pennyarcade/minidragon/schematics/Layout/A Register.kicad_sch

## KiCad design schematics/Layout/A Register.kicad_sch (2026-05-20)

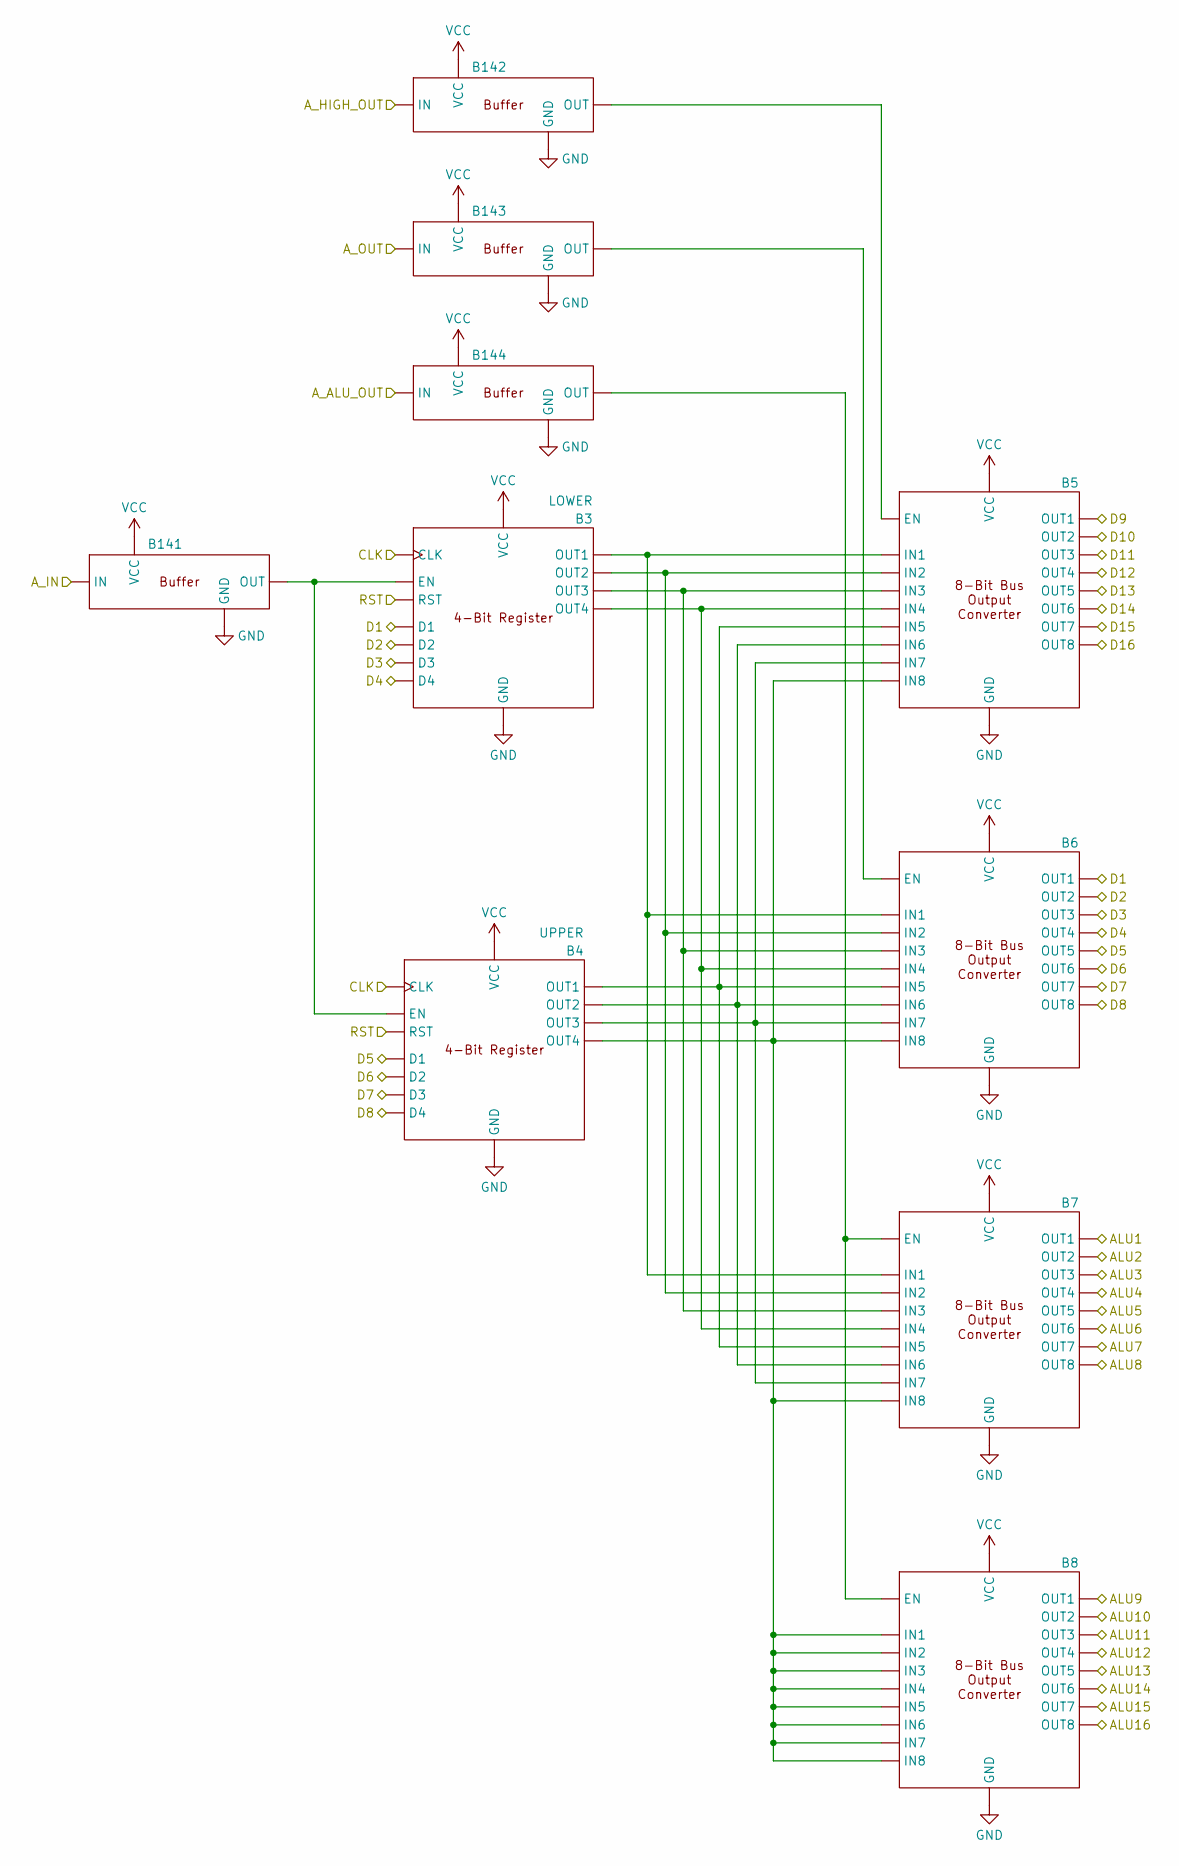
[picture p16: schematic A Register.kicad_sch]

Parts:
B3: LOWER
B4: UPPER
B5, B6, B7, B8, B141, B142, B143, B144: (no value)

Connections:
ALU1: B7.
ALU2: B7.
ALU3: B7.
ALU4: B7.
ALU5: B7.
ALU6: B7.
ALU7: B7.
ALU8: B7.
ALU9: B8.
ALU10: B8.
ALU11: B8.
ALU12: B8.
ALU13: B8.
ALU14: B8.
ALU15: B8.
ALU16: B8.
A_ALU_OUT: B144.
A_HIGH_OUT: B142.
A_IN: B141.
A_OUT: B143.
CLK: B3., B4.
D1: B3., B6.
D2: B3., B6.
D3: B3., B6.
D4: B3., B6.
D5: B4., B6.
D6: B4., B6.
D7: B4., B6.
D8: B4., B6.
D9: B5.
D10: B5.
D11: B5.
D12: B5.
D13: B5.
D14: B5.
D15: B5.
D16: B5.
GND: B3., B4., B5., B6., B7., B8., B141., B142., B143., B144.
unnamed: B3., B5., B6., B7.
unnamed: B4., B5., B6., B7., B8.
unnamed: B3., B4., B141.
unnamed: B5., B142.
unnamed: B6., B143.
unnamed: B7., B8., B144.
RST: B3., B4.
VCC: B3., B4., B5., B6., B7., B8., B141., B142., B143., B144.
