pennyarcade/minidragon/schematics/Layout/ALU Add Circuit.kicad_sch

## KiCad design schematics/Layout/ALU Add Circuit.kicad_sch (2026-05-20)

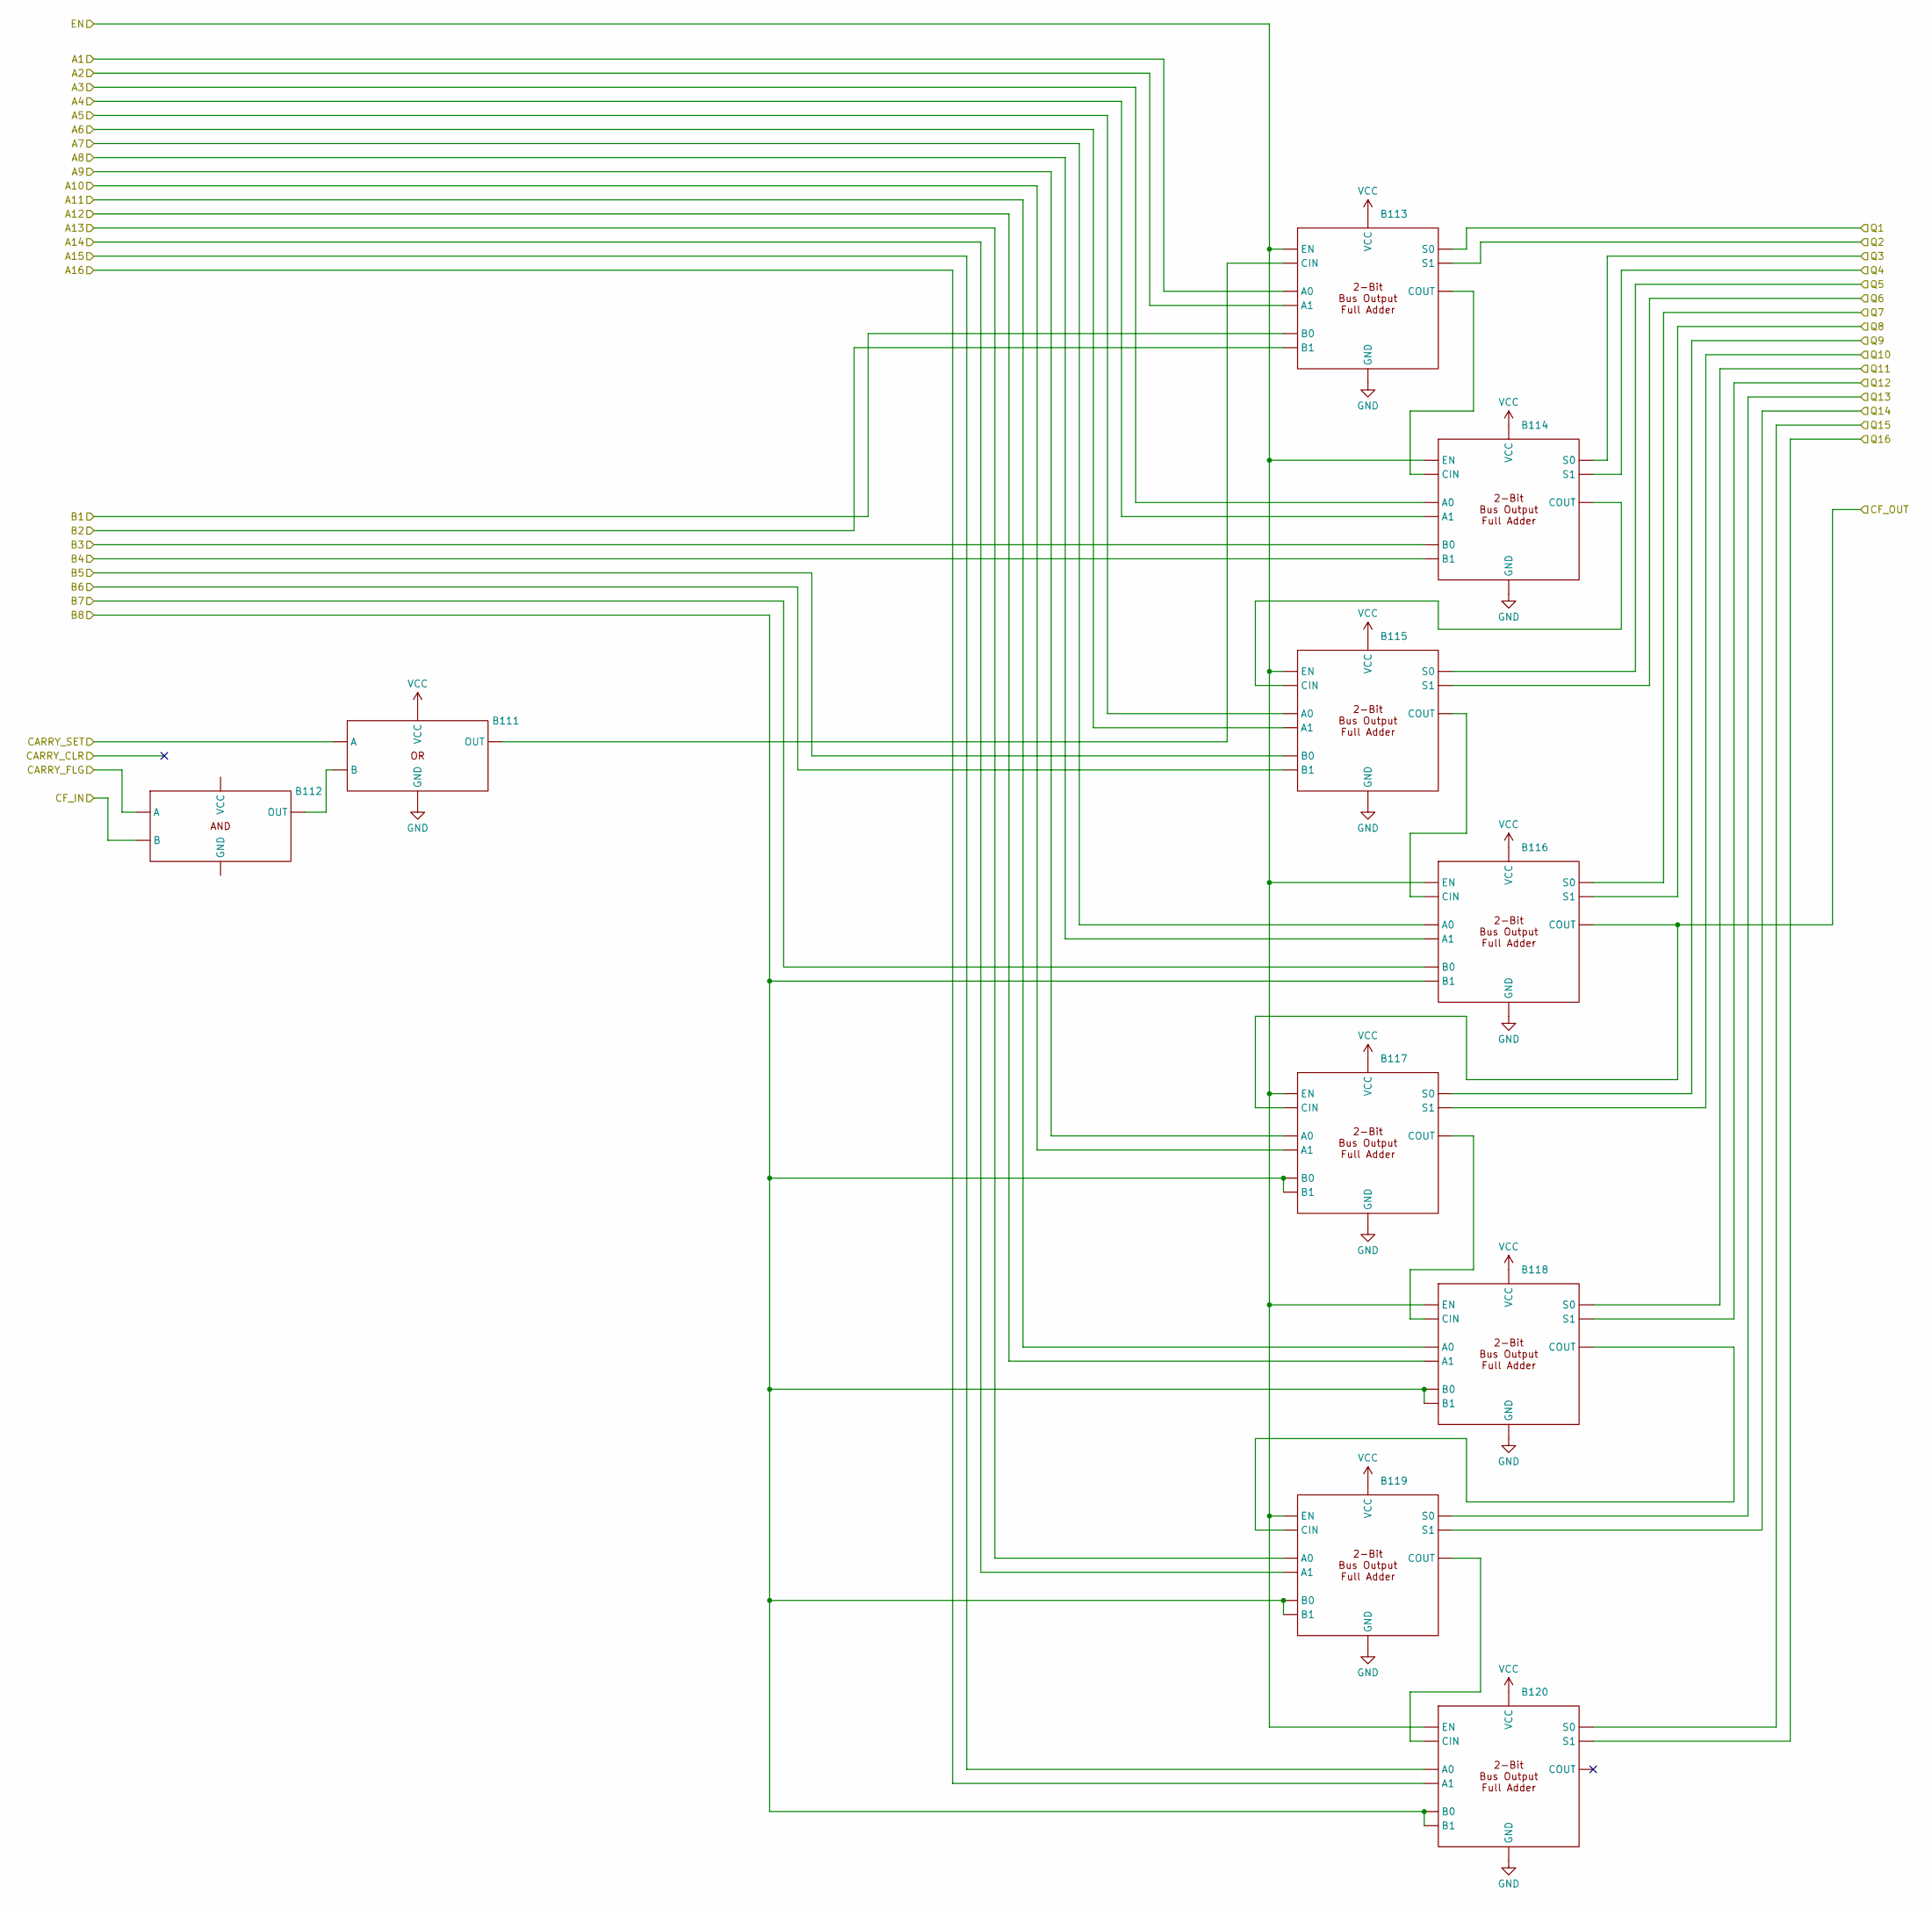
[picture p18: schematic ALU Add Circuit.kicad_sch]

Parts:
B111, B112, B113, B114, B115, B116, B117, B118, B119, B120: (no value)

Connections:
A1: B113.
A2: B113.
A3: B114.
A4: B114.
A5: B115.
A6: B115.
A7: B116.
A8: B116.
A9: B117.
A10: B117.
A11: B118.
A12: B118.
A13: B119.
A14: B119.
A15: B120.
A16: B120.
B1: B113.
B2: B113.
B3: B114.
B4: B114.
B5: B115.
B6: B115.
B7: B116.
B8: B116., B117., B118., B119., B120.
CARRY_FLG: B112.
CARRY_SET: B111.
CF_IN: B112.
CF_OUT: B116., B117.
EN: B113., B114., B115., B116., B117., B118., B119., B120.
GND: B111., B113., B114., B115., B116., B117., B118., B119., B120.
unnamed: B111., B112., B113.
unnamed: B113., B114.
unnamed: B114., B115.
unnamed: B115., B116.
unnamed: B117., B118.
unnamed: B118., B119.
unnamed: B119., B120.
Q1: B113.
Q2: B113.
Q3: B114.
Q4: B114.
Q5: B115.
Q6: B115.
Q7: B116.
Q8: B116.
Q9: B117.
Q10: B117.
Q11: B118.
Q12: B118.
Q13: B119.
Q14: B119.
Q15: B120.
Q16: B120.
VCC: B111., B113., B114., B115., B116., B117., B118., B119., B120.
