pennyarcade/minidragon/schematics/Layout/ALU Boolean Circuit.kicad_sch

## KiCad design schematics/Layout/ALU Boolean Circuit.kicad_sch (2026-05-20)

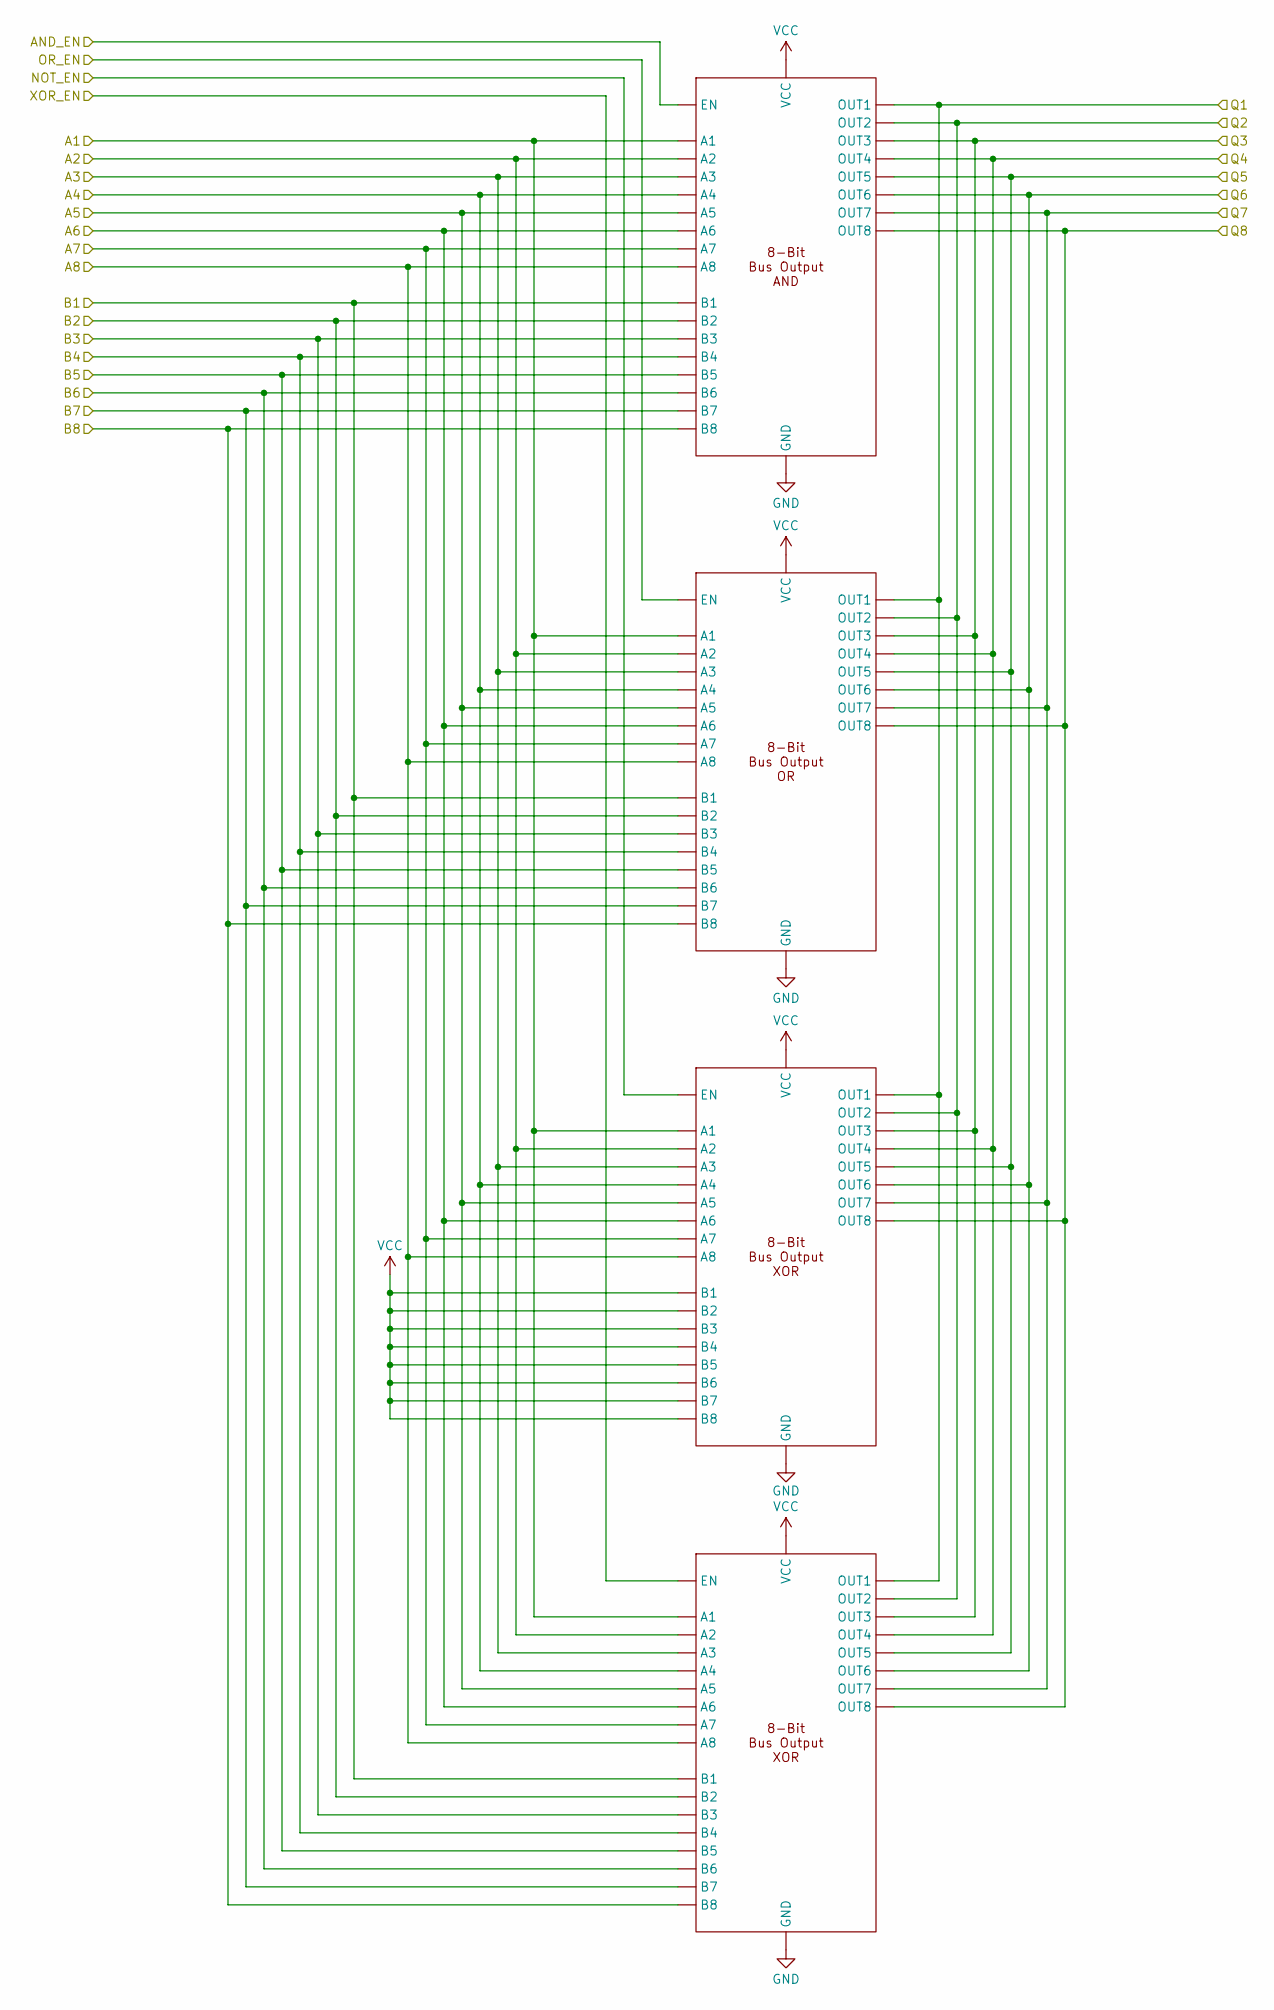
[picture p19: schematic ALU Boolean Circuit.kicad_sch]

Parts:
B158, B159, B160, B161: (no value)

Connections:
A1: B158., B159., B160., B161.
A2: B158., B159., B160., B161.
A3: B158., B159., B160., B161.
A4: B158., B159., B160., B161.
A5: B158., B159., B160., B161.
A6: B158., B159., B160., B161.
A7: B158., B159., B160., B161.
A8: B158., B159., B160., B161.
AND_EN: B158.
B1: B158., B159., B161.
B2: B158., B159., B161.
B3: B158., B159., B161.
B4: B158., B159., B161.
B5: B158., B159., B161.
B6: B158., B159., B161.
B7: B158., B159., B161.
B8: B158., B159., B161.
GND: B158., B159., B160., B161.
NOT_EN: B160.
OR_EN: B159.
Q1: B158., B159., B160., B161.
Q2: B158., B159., B160., B161.
Q3: B158., B159., B160., B161.
Q4: B158., B159., B160., B161.
Q5: B158., B159., B160., B161.
Q6: B158., B159., B160., B161.
Q7: B158., B159., B160., B161.
Q8: B158., B159., B160., B161.
VCC: B158., B159., B160., B161.
XOR_EN: B161.
