pennyarcade/minidragon/schematics/Layout/ALU.kicad_sch

## KiCad design schematics/Layout/ALU.kicad_sch (2026-05-20)

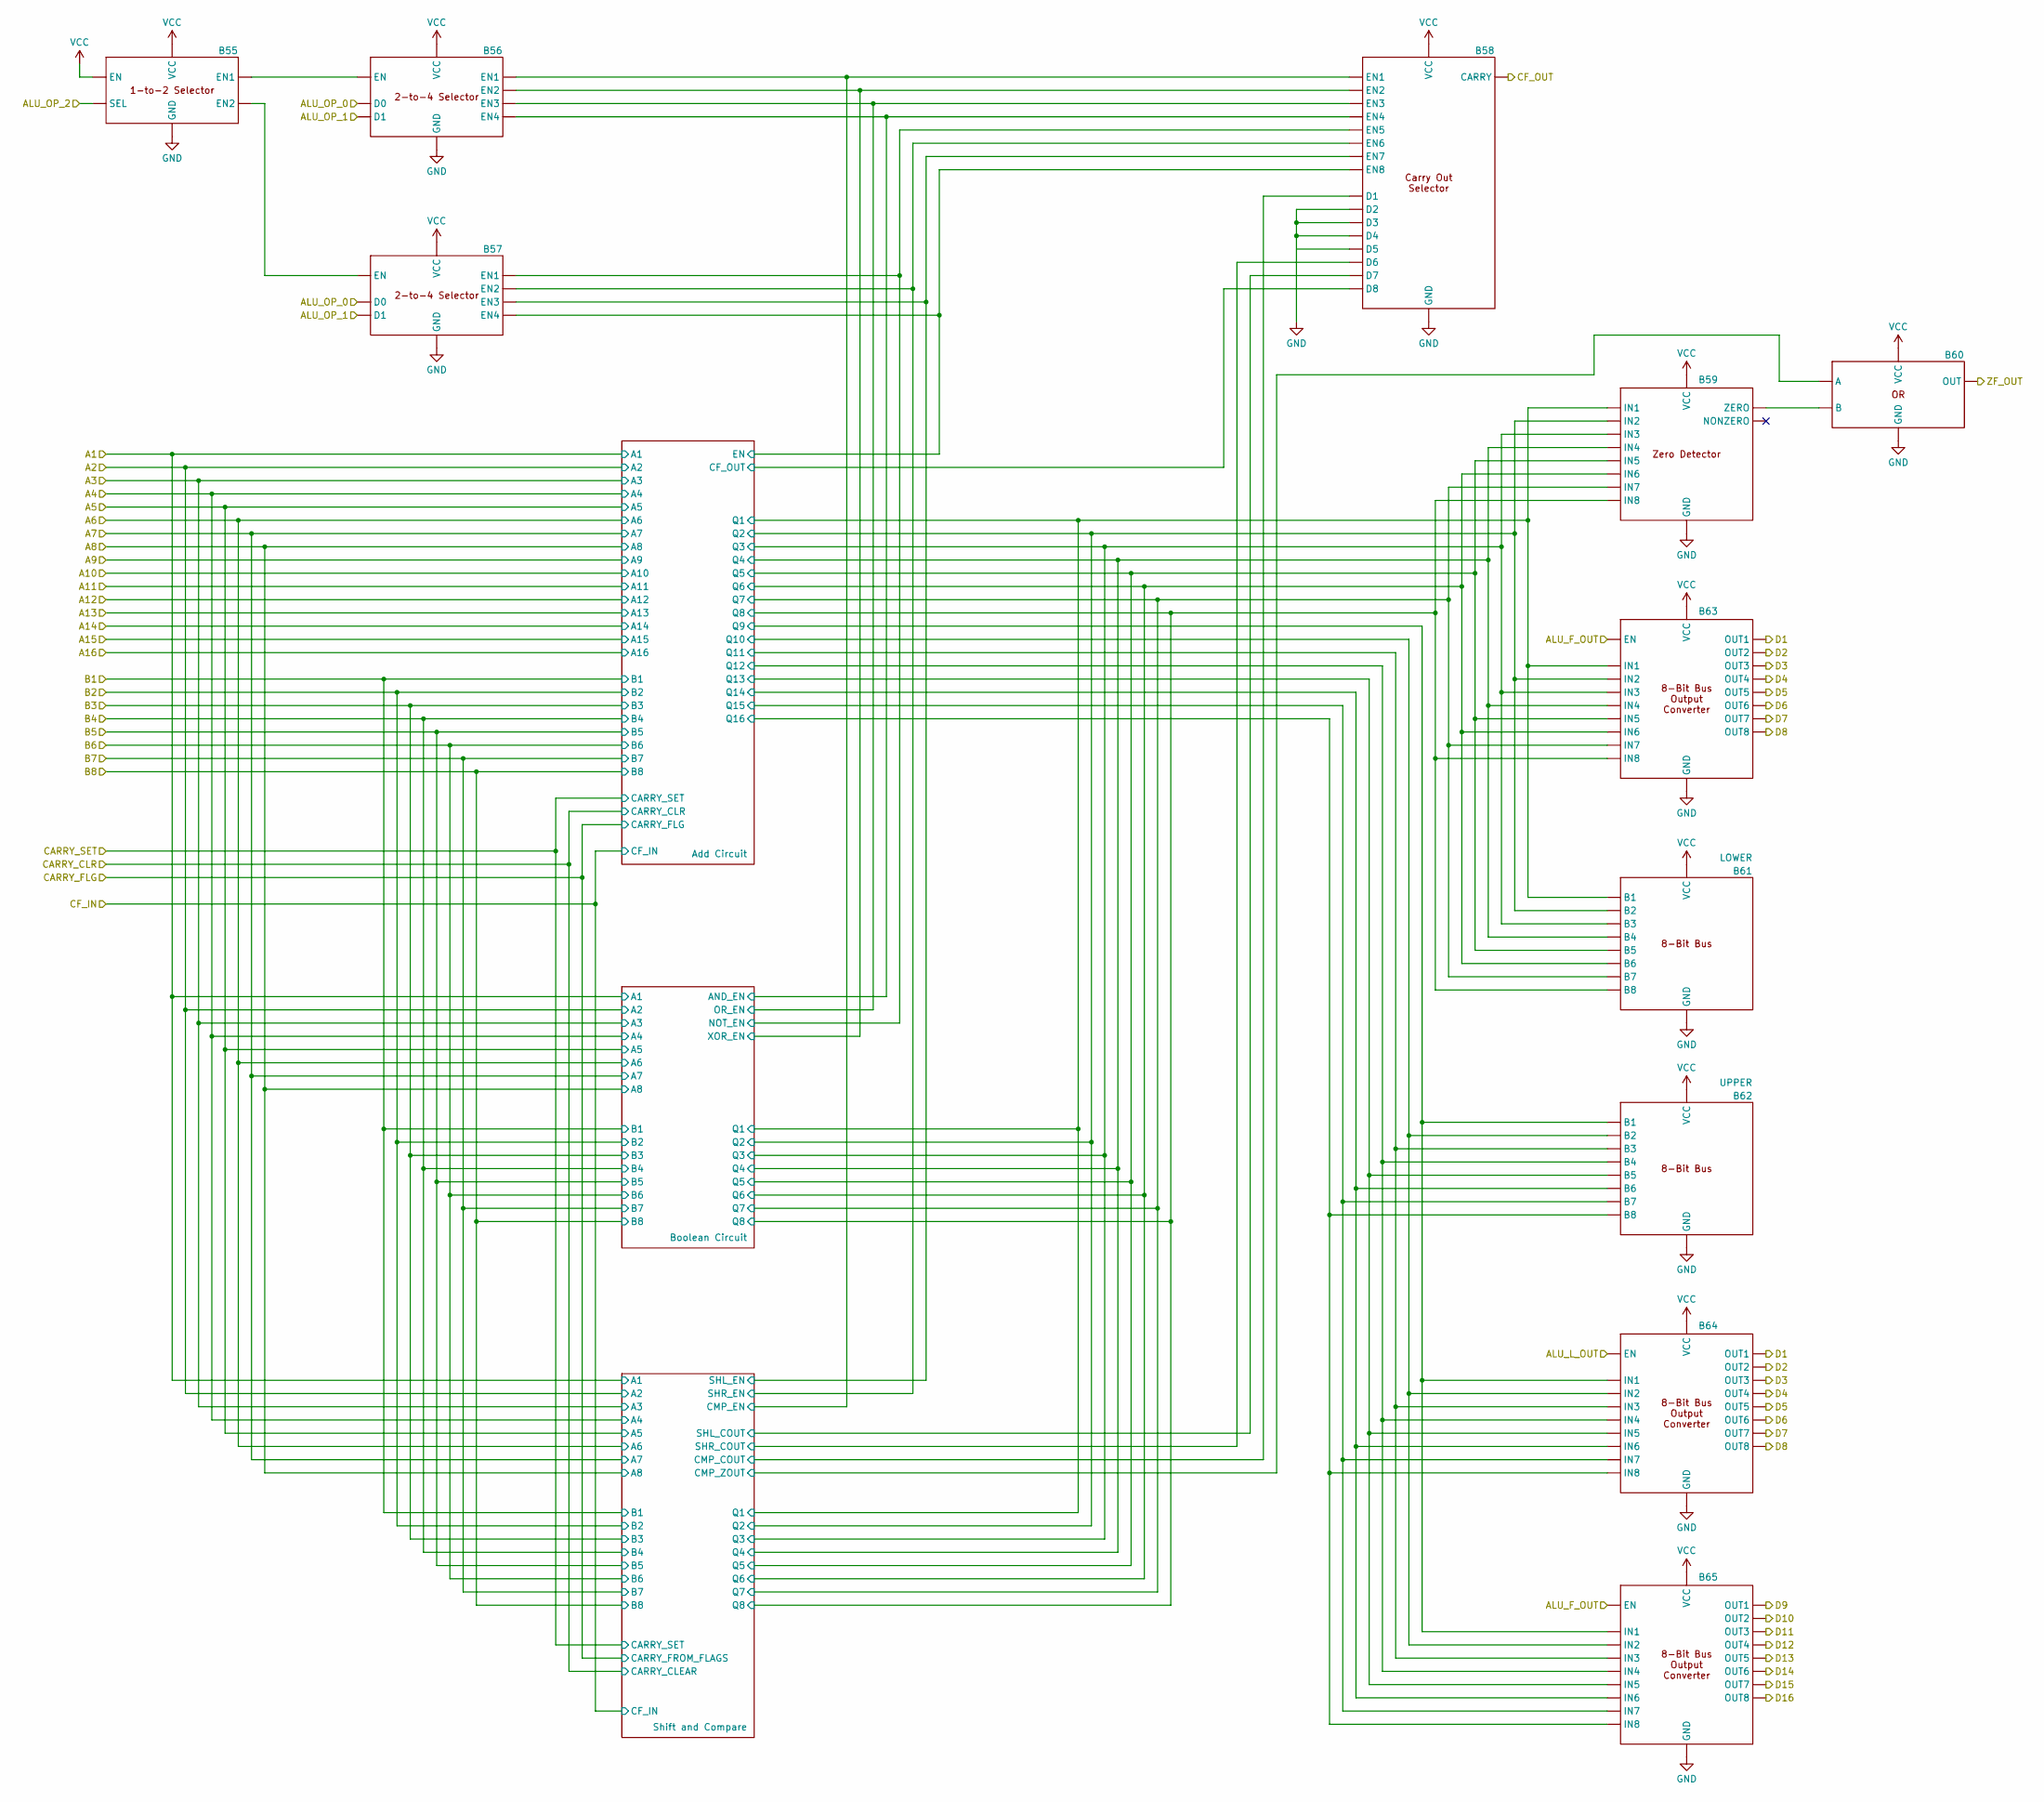
[picture p20: schematic ALU.kicad_sch]

Parts:
B55, B56, B57, B58, B59, B60, B63, B64, B65: (no value)
B61: LOWER
B62: UPPER

Connections:
ALU_F_OUT: B63., B65.
ALU_L_OUT: B64.
ALU_OP_0: B56., B57.
ALU_OP_1: B56., B57.
ALU_OP_2: B55.
AND_EN: B56., B58.
CF_OUT: B58.
CMP_COUT: B58.
CMP_EN: B56., B58.
CMP_ZOUT: B60.
D1: B63., B64.
D2: B63., B64.
D3: B63., B64.
D4: B63., B64.
D5: B63., B64.
D6: B63., B64.
D7: B63., B64.
D8: B63., B64.
D9: B65.
D10: B65.
D11: B65.
D12: B65.
D13: B65.
D14: B65.
D15: B65.
D16: B65.
EN: B57., B58.
GND: B55., B56., B57., B58., B59., B60., B61., B62., B63., B64., B65.
NOT_EN: B57., B58.
unnamed: B55., B56., B57.
unnamed: B59., B60.
OR_EN: B56., B58.
Q1: B59., B61., B63.
Q2: B59., B61., B63.
Q3: B59., B61., B63.
Q4: B59., B61., B63.
Q5: B59., B61., B63.
Q6: B59., B61., B63.
Q7: B59., B61., B63.
Q8: B59., B61., B63.
Q9: B62., B64., B65.
Q10: B62., B64., B65.
Q11: B62., B64., B65.
Q12: B62., B64., B65.
Q13: B62., B64., B65.
Q14: B62., B64., B65.
Q15: B62., B64., B65.
Q16: B62., B64., B65.
SHL_COUT: B58.
SHL_EN: B57., B58.
SHR_COUT: B58.
SHR_EN: B57., B58.
VCC: B55., B56., B57., B58., B59., B60., B61., B62., B63., B64., B65.
XOR_EN: B56., B58.
ZF_OUT: B60.
