pennyarcade/minidragon/schematics/Layout/B Register.kicad_sch

## KiCad design schematics/Layout/B Register.kicad_sch (2026-05-20)

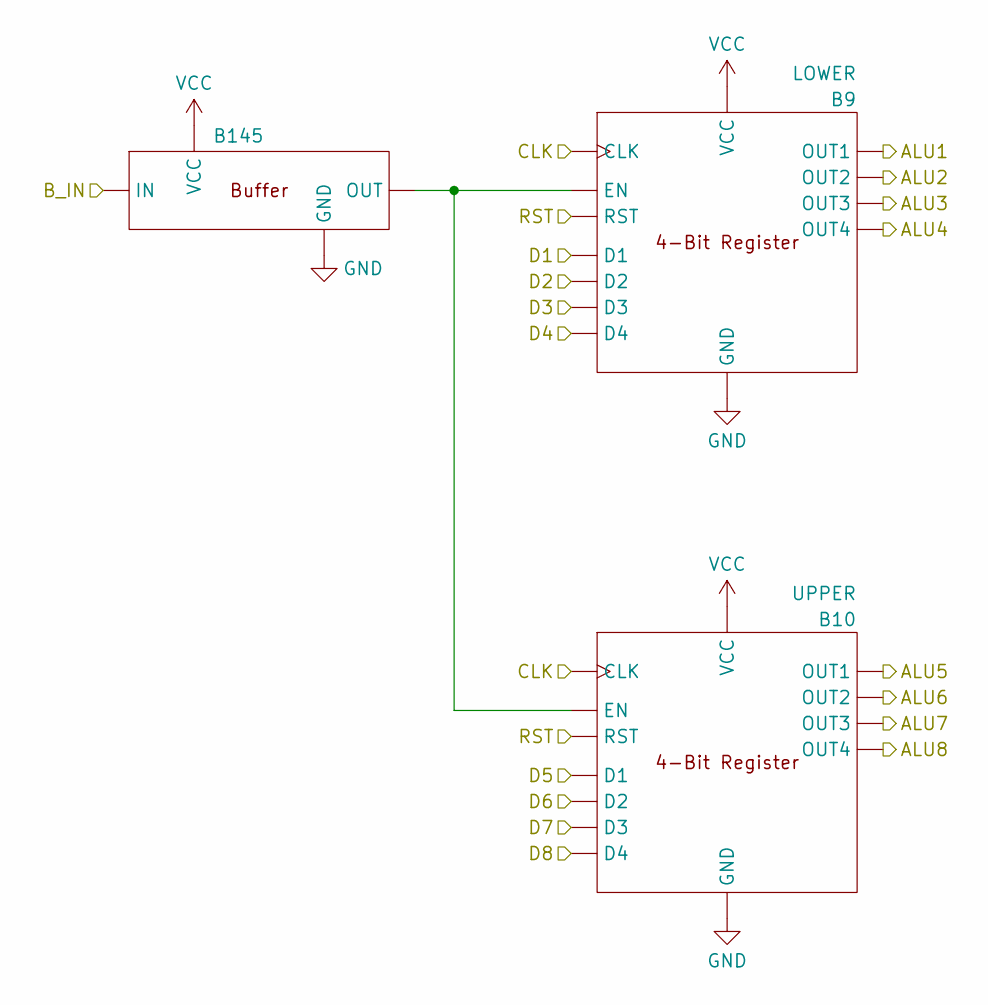
[picture p22: schematic B Register.kicad_sch]

Parts:
B9: LOWER
B10: UPPER
B145: (no value)

Connections:
ALU1: B9.
ALU2: B9.
ALU3: B9.
ALU4: B9.
ALU5: B10.
ALU6: B10.
ALU7: B10.
ALU8: B10.
B_IN: B145.
CLK: B9., B10.
D1: B9.
D2: B9.
D3: B9.
D4: B9.
D5: B10.
D6: B10.
D7: B10.
D8: B10.
GND: B9., B10., B145.
unnamed: B9., B10., B145.
RST: B9., B10.
VCC: B9., B10., B145.
