pennyarcade/minidragon/schematics/Layout/Data Bus.kicad_sch

## KiCad design schematics/Layout/Data Bus.kicad_sch (2026-05-20)

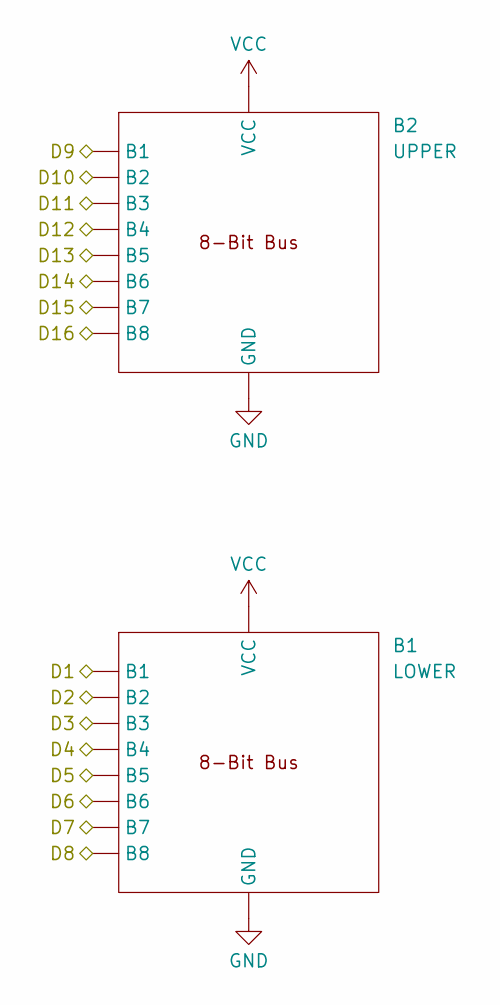
[picture p24: schematic Data Bus.kicad_sch]

Parts:
B1: LOWER
B2: UPPER

Connections:
D1: B1.
D2: B1.
D3: B1.
D4: B1.
D5: B1.
D6: B1.
D7: B1.
D8: B1.
D9: B2.
D10: B2.
D11: B2.
D12: B2.
D13: B2.
D14: B2.
D15: B2.
D16: B2.
GND: B1., B2.
VCC: B1., B2.
