pennyarcade/minidragon/schematics/Layout/Decoder Combinatorial Logic and ROM Boards.kicad_sch

## KiCad design schematics/Layout/Decoder Combinatorial Logic and ROM Boards.kicad_sch (2026-05-20)

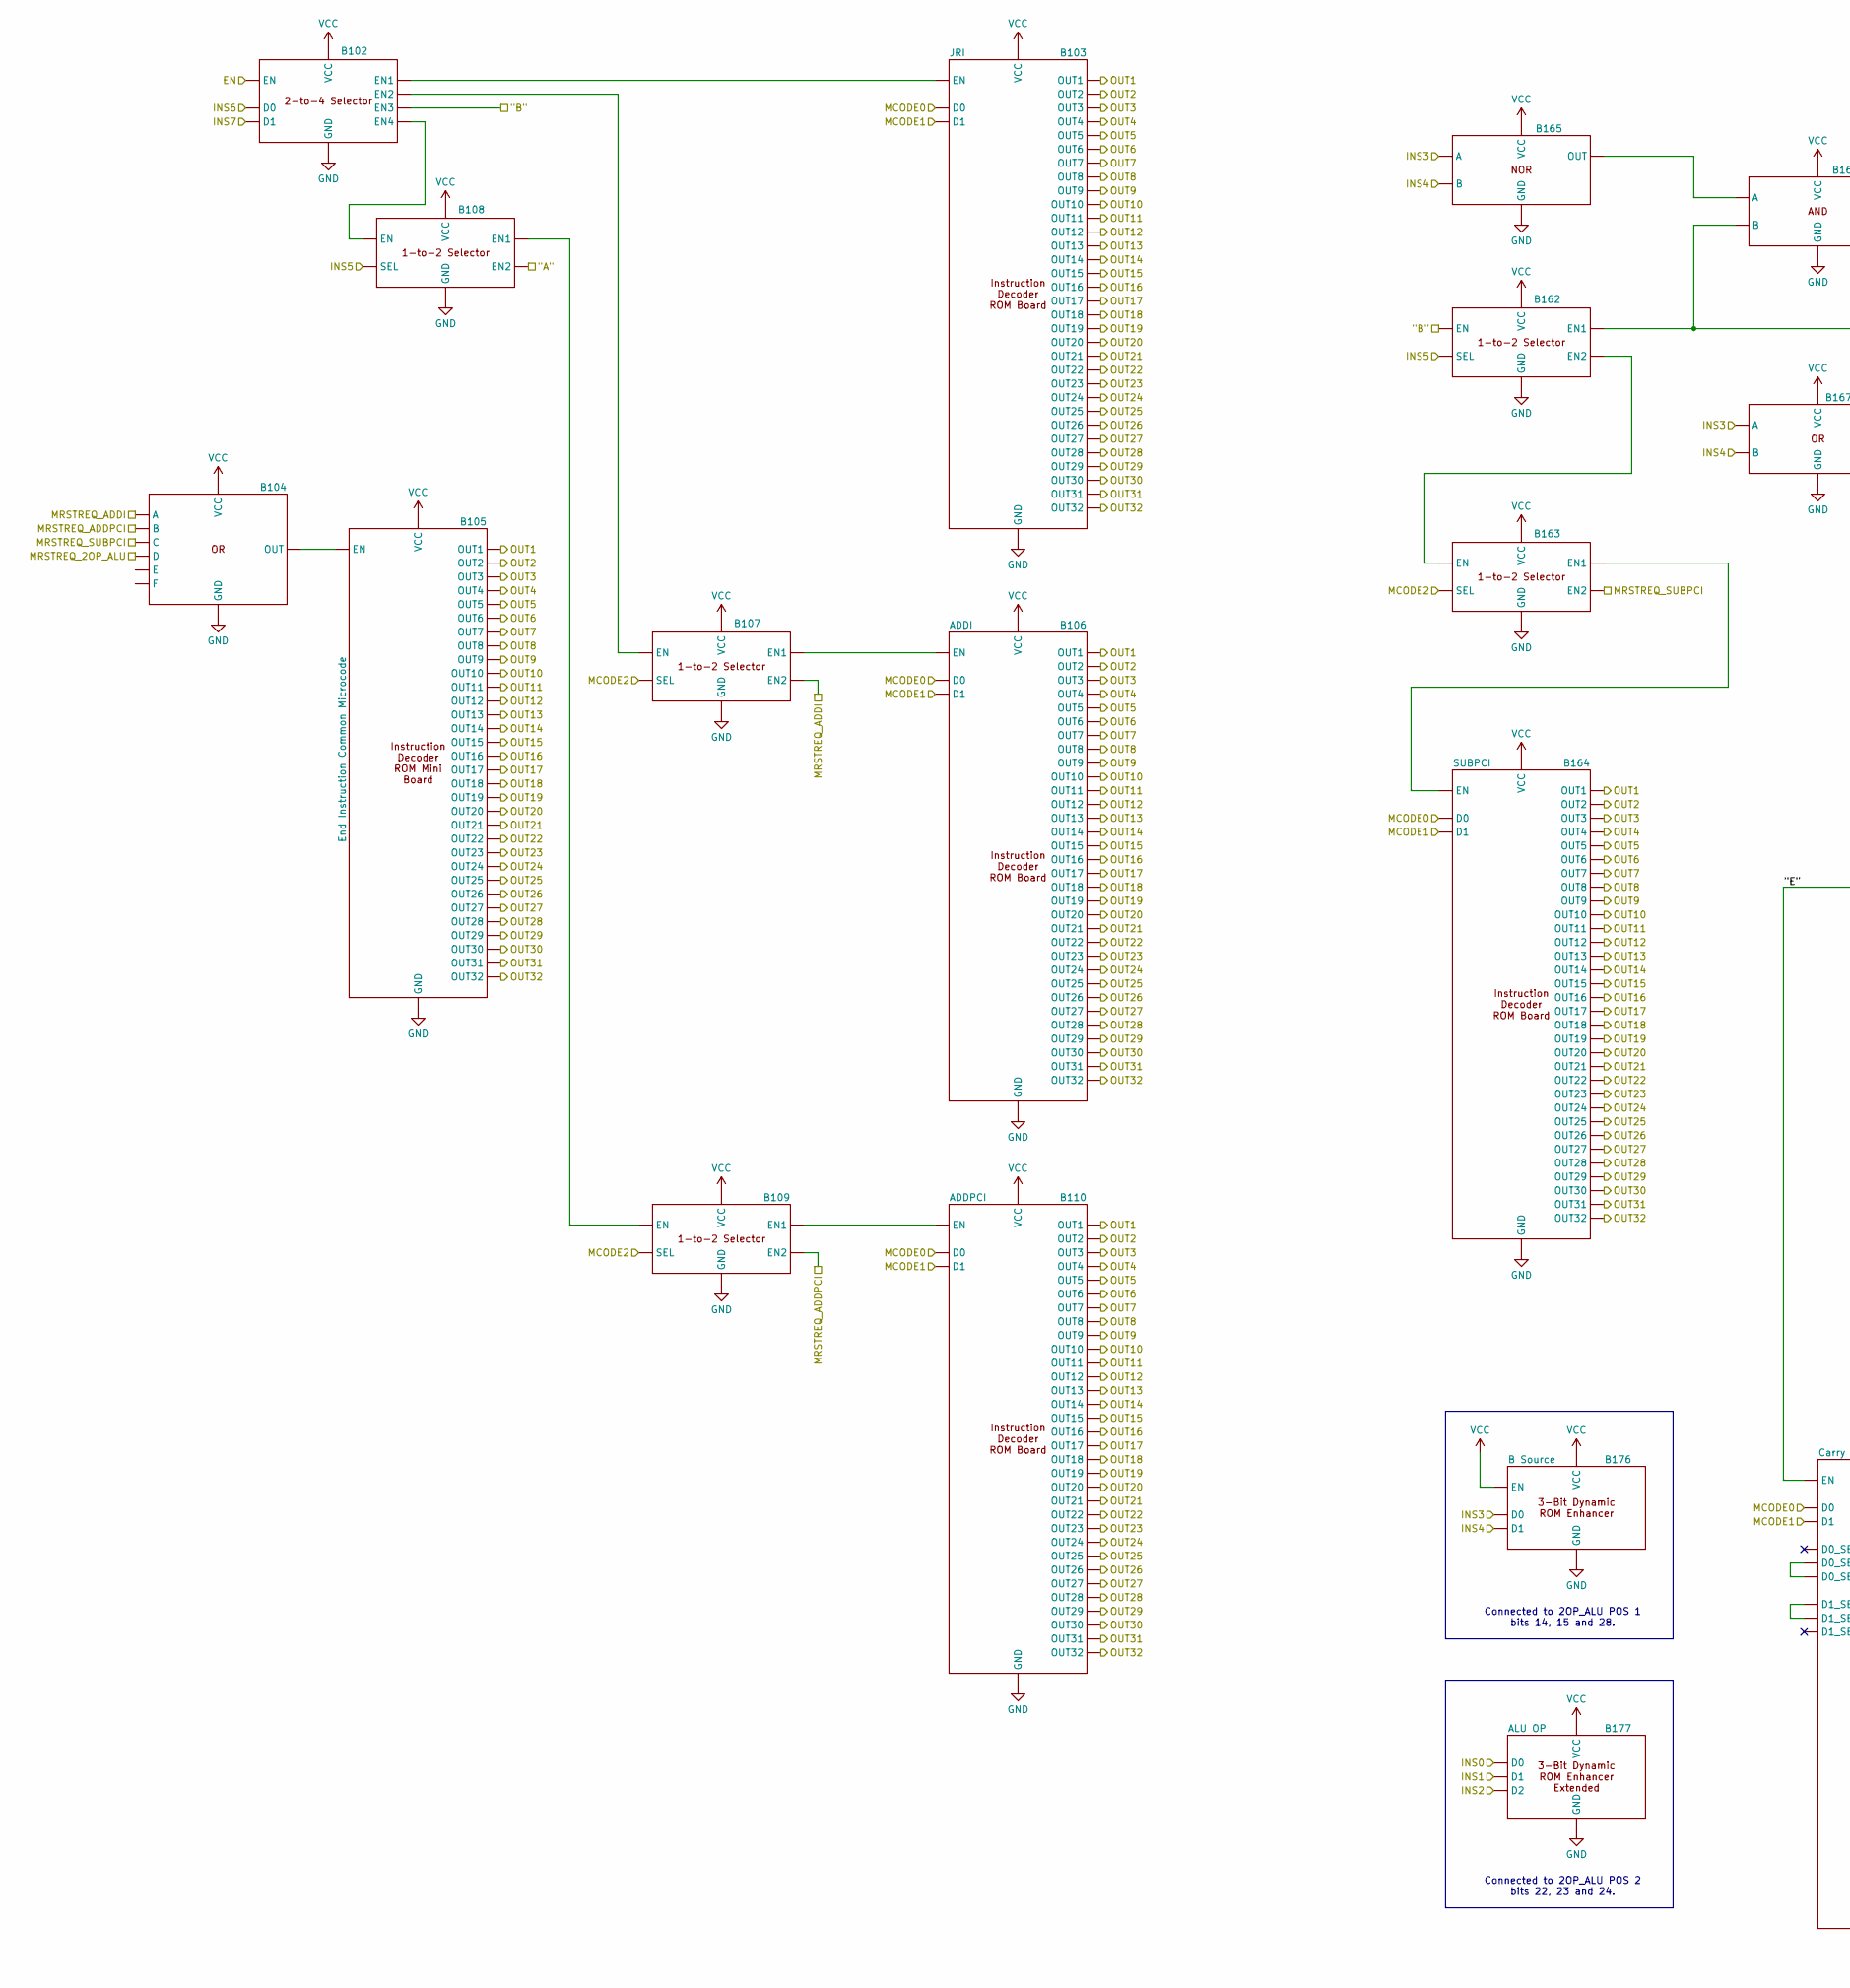
[picture p25: schematic Decoder Combinatorial Logic and ROM Boards.kicad_sch, part in row 1, column 1]

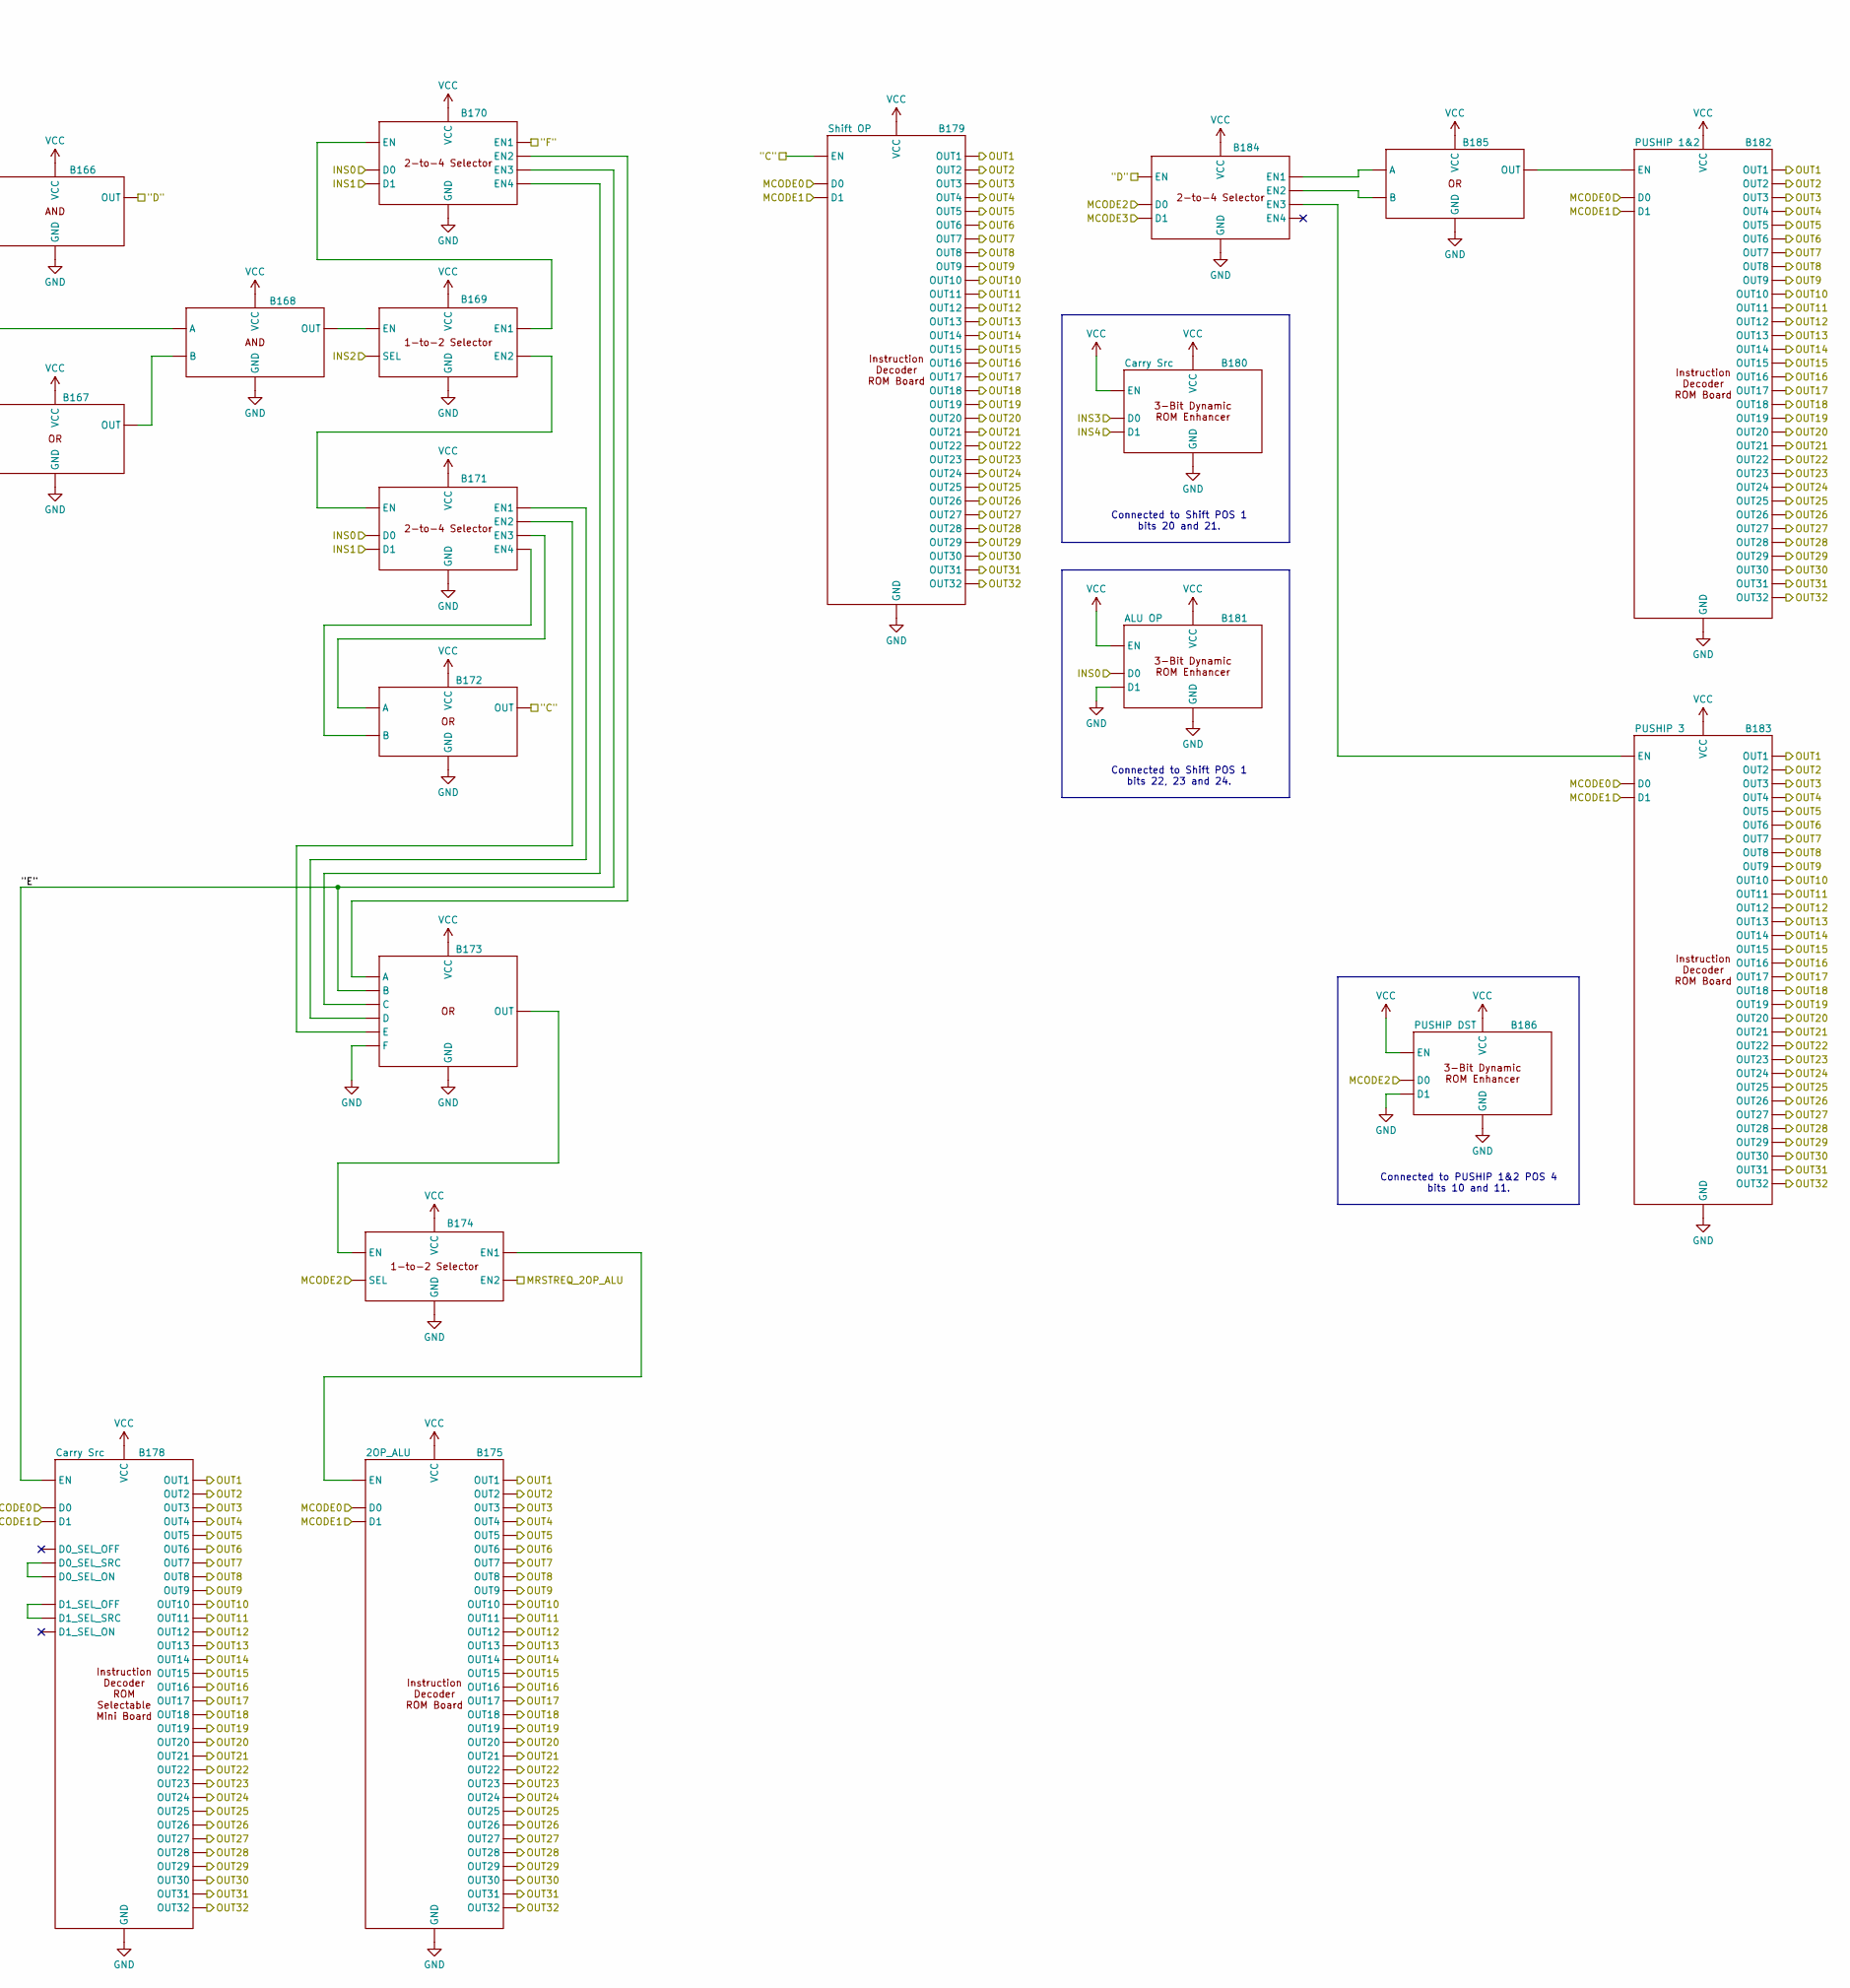
[picture p26: schematic Decoder Combinatorial Logic and ROM Boards.kicad_sch, part in row 1, column 2]

Parts:
B102, B104, B107, B108, B109, B162, B163, B165, B166, B167, B168, B169, B170, B171, B172, B173, B174, B184, B185: (no value)
B103: JRI
B105: End Instruction Common Microcode
B106: ADDI
B110: ADDPCI
B164: SUBPCI
B175: 2OP_ALU
B176: B Source
B177, B181: ALU OP
B178, B180: Carry Src
B179: Shift OP
B182: PUSHIP 1&2
B183: PUSHIP 3
B186: PUSHIP DST

Connections:
"A": B108.
"B": B102., B162.
"C": B172., B179.
"D": B166., B184.
"E": B170., B173., B178.
"F": B170.
EN: B102.
GND: B102., B103., B104., B105., B106., B107., B108., B109., B110., B162., B163., B164., B165., B166., B167., B168., B169., B170., B171., B172., B173., B174., B175., B176., B177., B178., B179., B180., B181., B182., B183., B184., B185., B186.
INS0: B170., B171., B177., B181.
INS1: B170., B171., B177.
INS2: B169., B177.
INS3: B165., B167., B176., B180.
INS4: B165., B167., B176., B180.
INS5: B108., B162.
INS6: B102.
INS7: B102.
MCODE0: B103., B106., B110., B164., B175., B178., B179., B182., B183.
MCODE1: B103., B106., B110., B164., B175., B178., B179., B182., B183.
MCODE2: B107., B109., B163., B174., B184., B186.
MCODE3: B184.
MRSTREQ_2OP_ALU: B104., B174.
MRSTREQ_ADDI: B104., B107.
MRSTREQ_ADDPCI: B104., B109.
MRSTREQ_SUBPCI: B104., B163.
unnamed: B102., B103., B107., B108.
unnamed: B104., B105.
unnamed: B106., B107.
unnamed: B108., B109.
unnamed: B109., B110.
unnamed: B162., B163., B166., B168.
unnamed: B163., B164.
unnamed: B165., B166.
unnamed: B167., B168.
unnamed: B168., B169.
unnamed: B169., B170., B171.
unnamed: B170., B173.
unnamed: B171., B172., B173.
unnamed: B173., B174.
unnamed: B174., B175.
unnamed: B182., B185.
unnamed: B183., B184.
unnamed: B184., B185.
OUT1: B103., B105., B106., B110., B164., B175., B178., B179., B182., B183.
OUT2: B103., B105., B106., B110., B164., B175., B178., B179., B182., B183.
OUT3: B103., B105., B106., B110., B164., B175., B178., B179., B182., B183.
OUT4: B103., B105., B106., B110., B164., B175., B178., B179., B182., B183.
OUT5: B103., B105., B106., B110., B164., B175., B178., B179., B182., B183.
OUT6: B103., B105., B106., B110., B164., B175., B178., B179., B182., B183.
OUT7: B103., B105., B106., B110., B164., B175., B178., B179., B182., B183.
OUT8: B103., B105., B106., B110., B164., B175., B178., B179., B182., B183.
OUT9: B103., B105., B106., B110., B164., B175., B178., B179., B182., B183.
OUT10: B103., B105., B106., B110., B164., B175., B178., B179., B182., B183.
OUT11: B103., B105., B106., B110., B164., B175., B178., B179., B182., B183.
OUT12: B103., B105., B106., B110., B164., B175., B178., B179., B182., B183.
OUT13: B103., B105., B106., B110., B164., B175., B178., B179., B182., B183.
OUT14: B103., B105., B106., B110., B164., B175., B178., B179., B182., B183.
OUT15: B103., B105., B106., B110., B164., B175., B178., B179., B182., B183.
OUT16: B103., B105., B106., B110., B164., B175., B178., B179., B182., B183.
OUT17: B103., B105., B106., B110., B164., B175., B178., B179., B182., B183.
OUT18: B103., B105., B106., B110., B164., B175., B178., B179., B182., B183.
OUT19: B103., B105., B106., B110., B164., B175., B178., B179., B182., B183.
OUT20: B103., B105., B106., B110., B164., B175., B178., B179., B182., B183.
OUT21: B103., B105., B106., B110., B164., B175., B178., B179., B182., B183.
OUT22: B103., B105., B106., B110., B164., B175., B178., B179., B182., B183.
OUT23: B103., B105., B106., B110., B164., B175., B178., B179., B182., B183.
OUT24: B103., B105., B106., B110., B164., B175., B178., B179., B182., B183.
OUT25: B103., B105., B106., B110., B164., B175., B178., B179., B182., B183.
OUT26: B103., B105., B106., B110., B164., B175., B178., B179., B182., B183.
OUT27: B103., B105., B106., B110., B164., B175., B178., B179., B182., B183.
OUT28: B103., B105., B106., B110., B164., B175., B178., B179., B182., B183.
OUT29: B103., B105., B106., B110., B164., B175., B178., B179., B182., B183.
OUT30: B103., B105., B106., B110., B164., B175., B178., B179., B182., B183.
OUT31: B103., B105., B106., B110., B164., B175., B178., B179., B182., B183.
OUT32: B103., B105., B106., B110., B164., B175., B178., B179., B182., B183.
VCC: B102., B103., B104., B105., B106., B107., B108., B109., B110., B162., B163., B164., B165., B166., B167., B168., B169., B170., B171., B172., B173., B174., B175., B176., B177., B178., B179., B180., B181., B182., B183., B184., B185., B186.

Notes on the sheet:
Connected to PUSHIP 1&2 POS 4 bits 10 and 11.
Connected to Shift POS 1 bits 20 and 21.
Connected to Shift POS 1 bits 22, 23 and 24.
Connected to 2OP_ALU POS 1 bits 14, 15 and 28.
Connected to 2OP_ALU POS 2 bits 22, 23 and 24.
