pennyarcade/minidragon/schematics/Layout/Flags Register.kicad_sch

## KiCad design schematics/Layout/Flags Register.kicad_sch (2026-05-20)

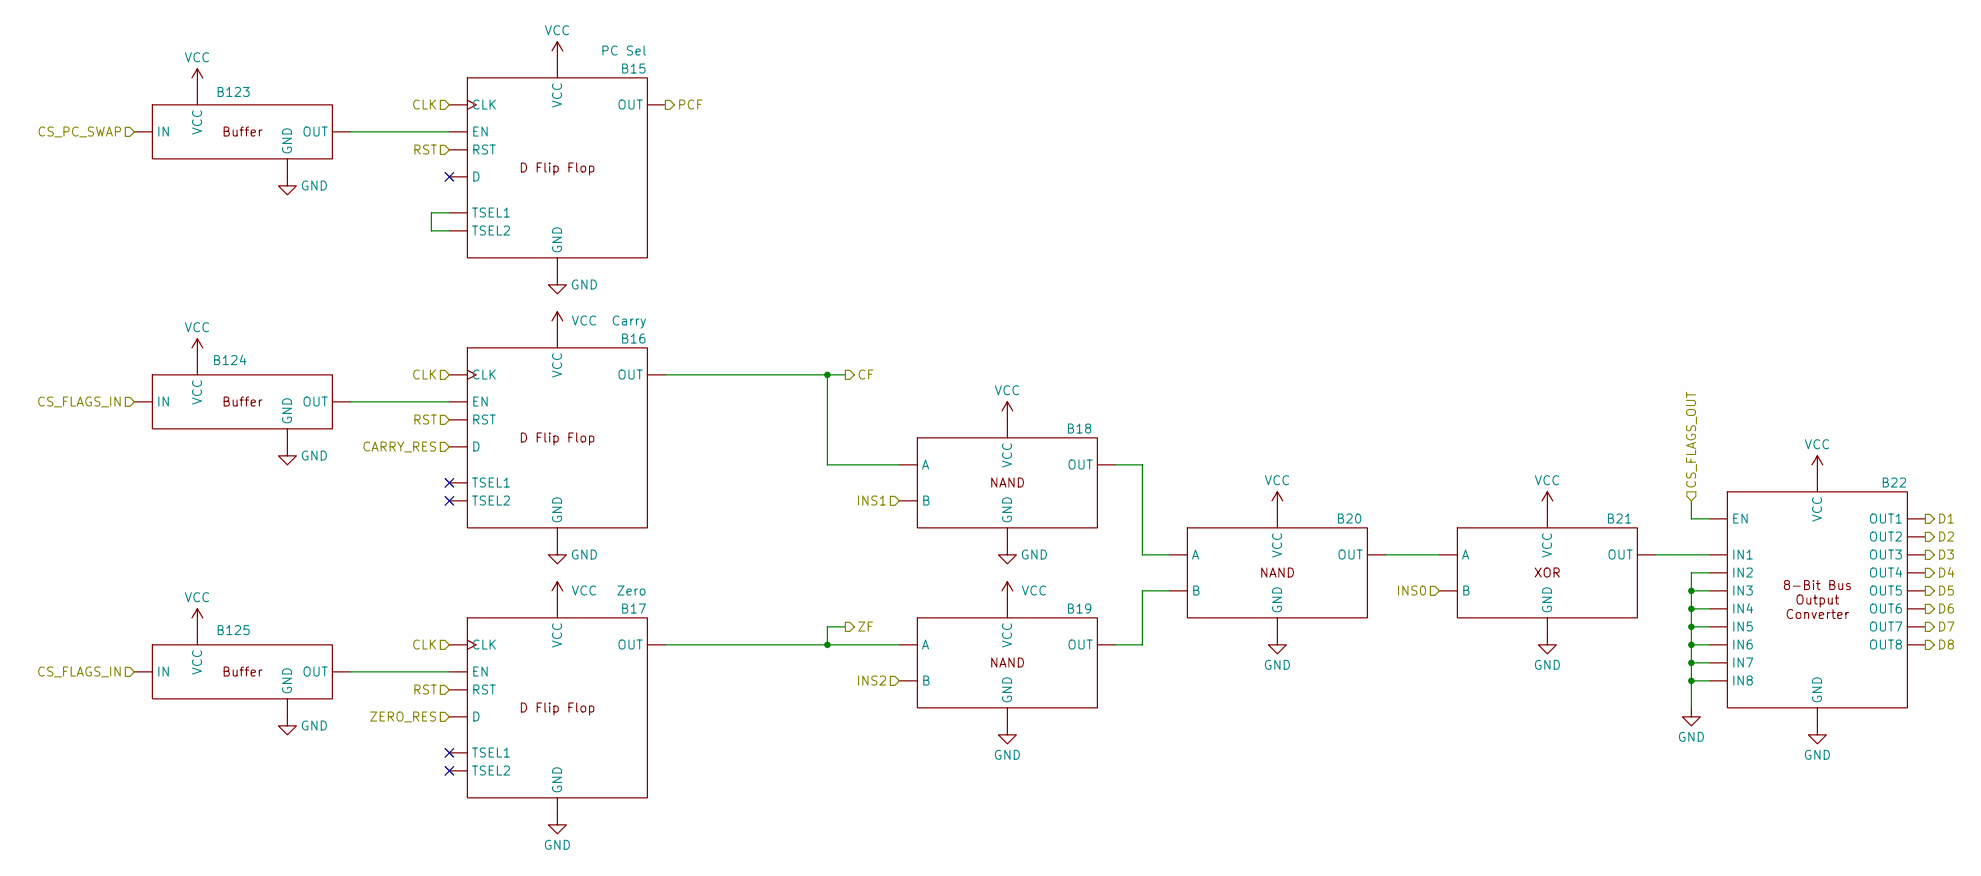
[picture p27: schematic Flags Register.kicad_sch]

Parts:
B15: PC Sel
B16: Carry
B17: Zero
B18, B19, B20, B21, B22, B123, B124, B125: (no value)

Connections:
CARRY_RES: B16.
CF: B16., B18.
CLK: B15., B16., B17.
CS_FLAGS_IN: B124., B125.
CS_FLAGS_OUT: B22.
CS_PC_SWAP: B123.
D1: B22.
D2: B22.
D3: B22.
D4: B22.
D5: B22.
D6: B22.
D7: B22.
D8: B22.
GND: B15., B16., B17., B18., B19., B20., B21., B22., B123., B124., B125.
INS0: B21.
INS1: B18.
INS2: B19.
unnamed: B18., B20.
unnamed: B19., B20.
unnamed: B20., B21.
unnamed: B21., B22.
unnamed: B15., B123.
unnamed: B16., B124.
unnamed: B17., B125.
PCF: B15.
RST: B15., B16., B17.
VCC: B15., B16., B17., B18., B19., B20., B21., B22., B123., B124., B125.
ZERO_RES: B17.
ZF: B17., B19.
