pennyarcade/minidragon/schematics/Layout/Instruction Register.kicad_sch

## KiCad design schematics/Layout/Instruction Register.kicad_sch (2026-05-20)

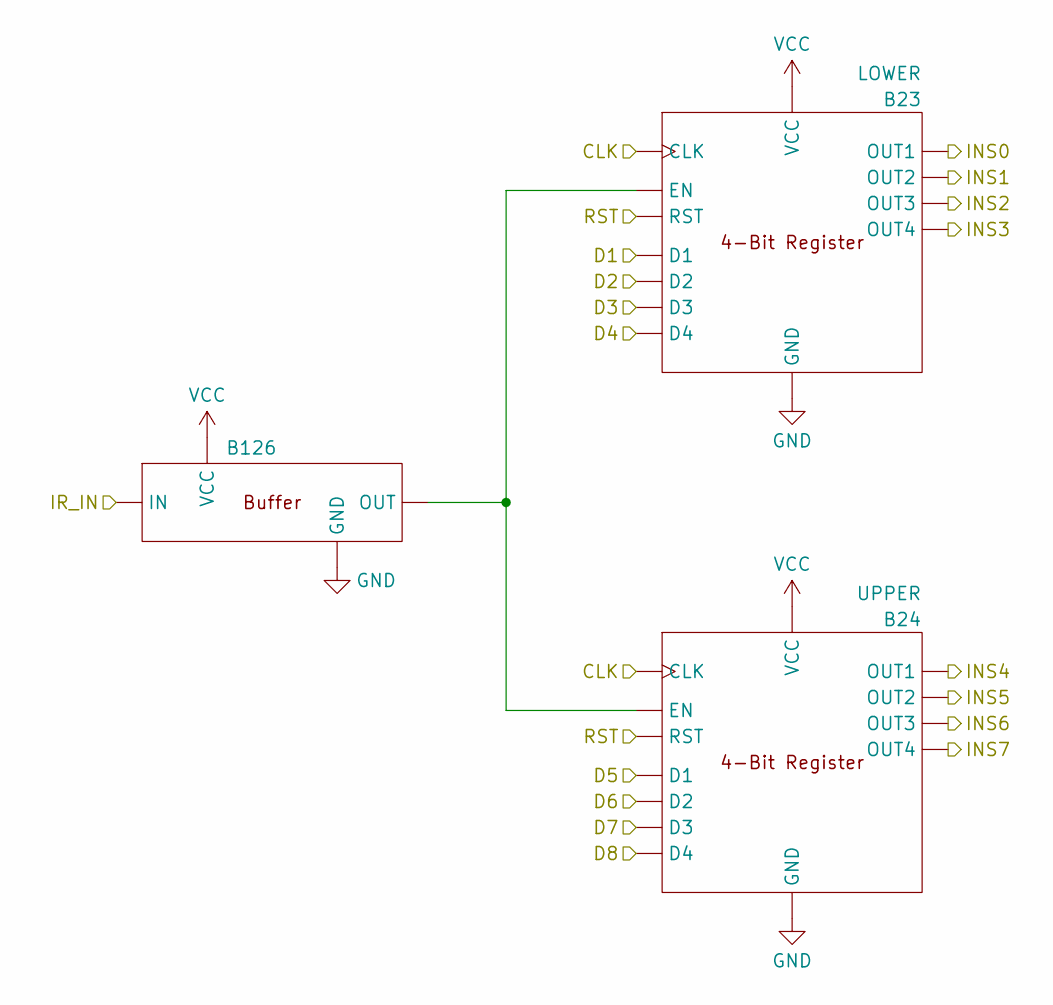
[picture p32: schematic Instruction Register.kicad_sch]

Parts:
B23: LOWER
B24: UPPER
B126: (no value)

Connections:
CLK: B23., B24.
D1: B23.
D2: B23.
D3: B23.
D4: B23.
D5: B24.
D6: B24.
D7: B24.
D8: B24.
GND: B23., B24., B126.
INS0: B23.
INS1: B23.
INS2: B23.
INS3: B23.
INS4: B24.
INS5: B24.
INS6: B24.
INS7: B24.
IR_IN: B126.
unnamed: B23., B24., B126.
RST: B23., B24.
VCC: B23., B24., B126.
