pennyarcade/minidragon/schematics/Layout/Microcode Counter.kicad_sch

## KiCad design schematics/Layout/Microcode Counter.kicad_sch (2026-05-20)

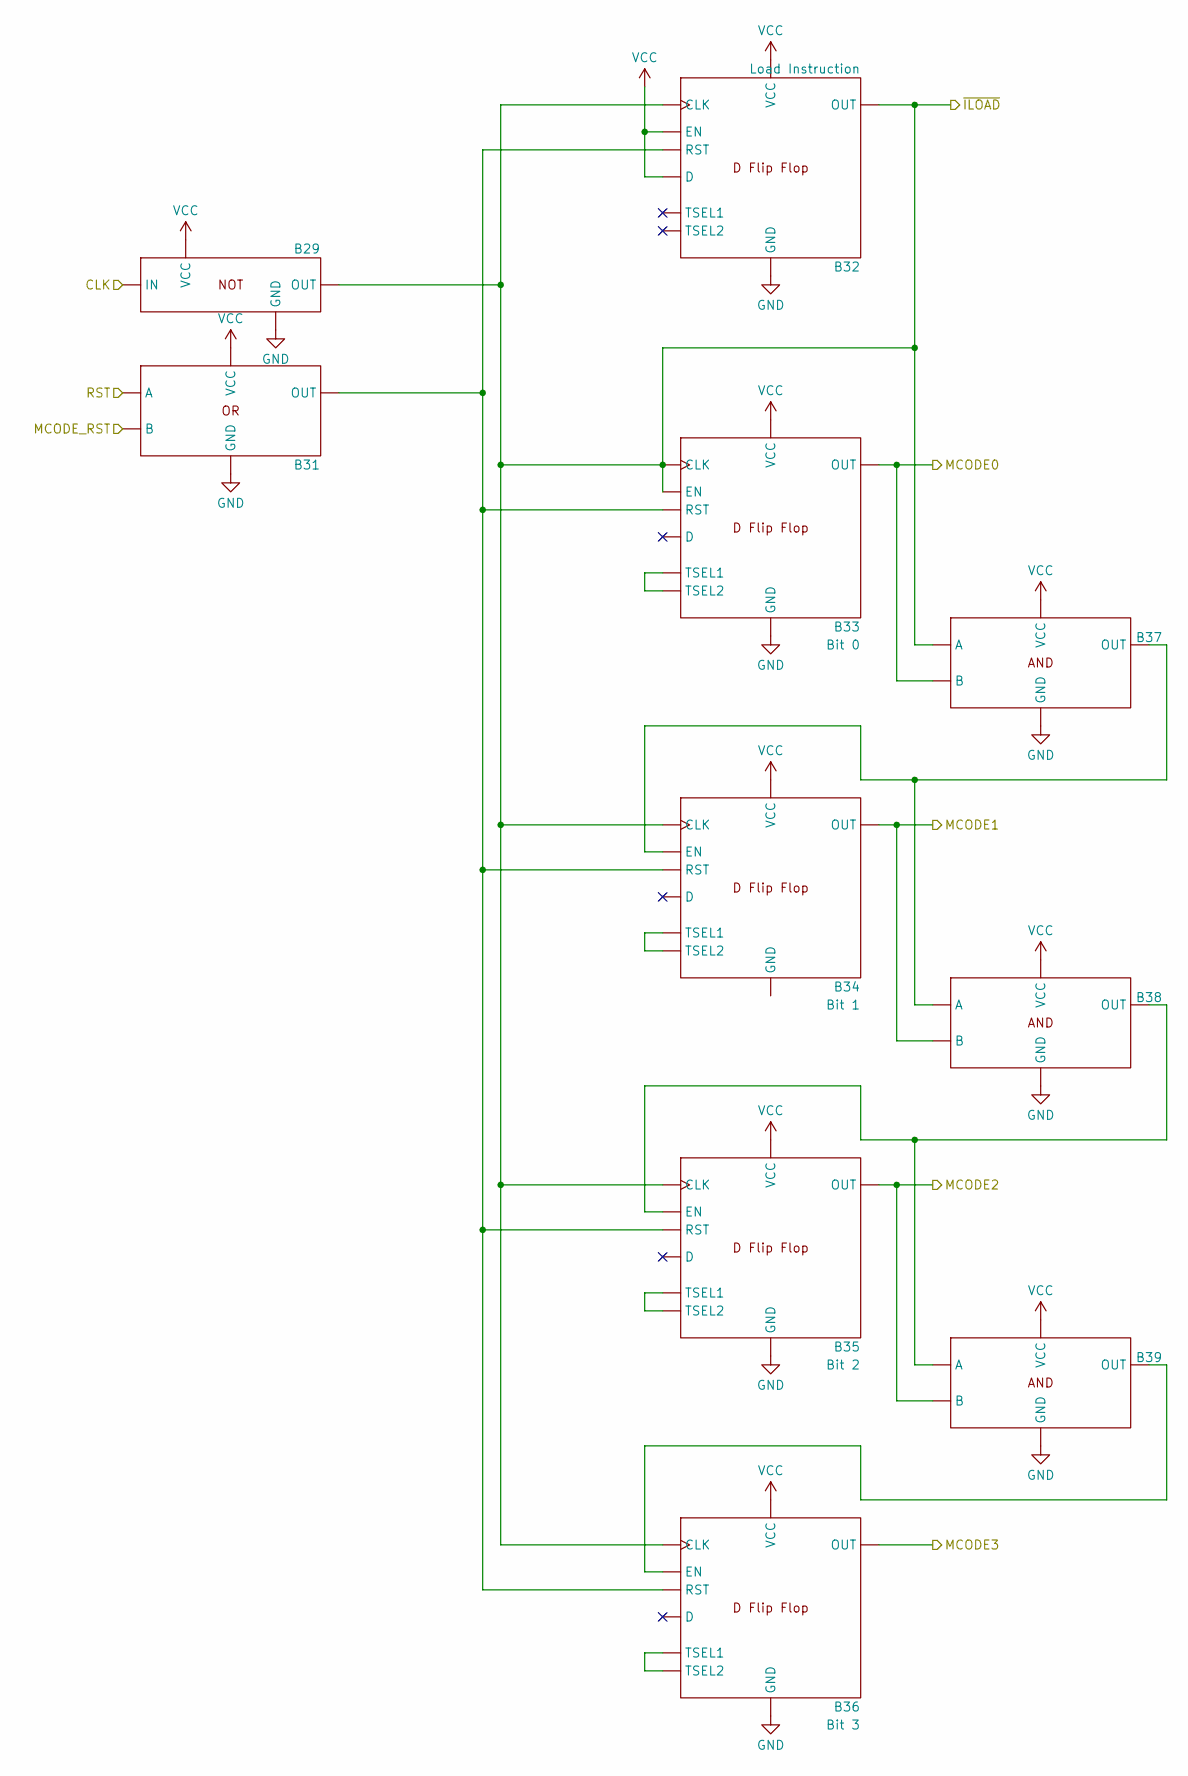
[picture p33: schematic Microcode Counter.kicad_sch]

Parts:
B29, B31, B37, B38, B39: (no value)
B32: Load Instruction
B33: Bit 0
B34: Bit 1
B35: Bit 2
B36: Bit 3

Connections:
CLK: B29.
GND: B29., B31., B32., B33., B35., B36., B37., B38., B39.
MCODE0: B33., B37.
MCODE1: B34., B38.
MCODE2: B35., B39.
MCODE3: B36.
MCODE_RST: B31.
unnamed: B31., B32., B33., B34., B35., B36.
unnamed: B34., B37., B38.
unnamed: B35., B38., B39.
unnamed: B36., B39.
RST: B31.
VCC: B29., B31., B32., B33., B34., B35., B36., B37., B38., B39.
~ILOAD: B29., B32., B33., B34., B35., B36., B37.
