pennyarcade/minidragon/schematics/Layout/SRAM Interface.kicad_sch

## KiCad design schematics/Layout/SRAM Interface.kicad_sch (2026-05-20)

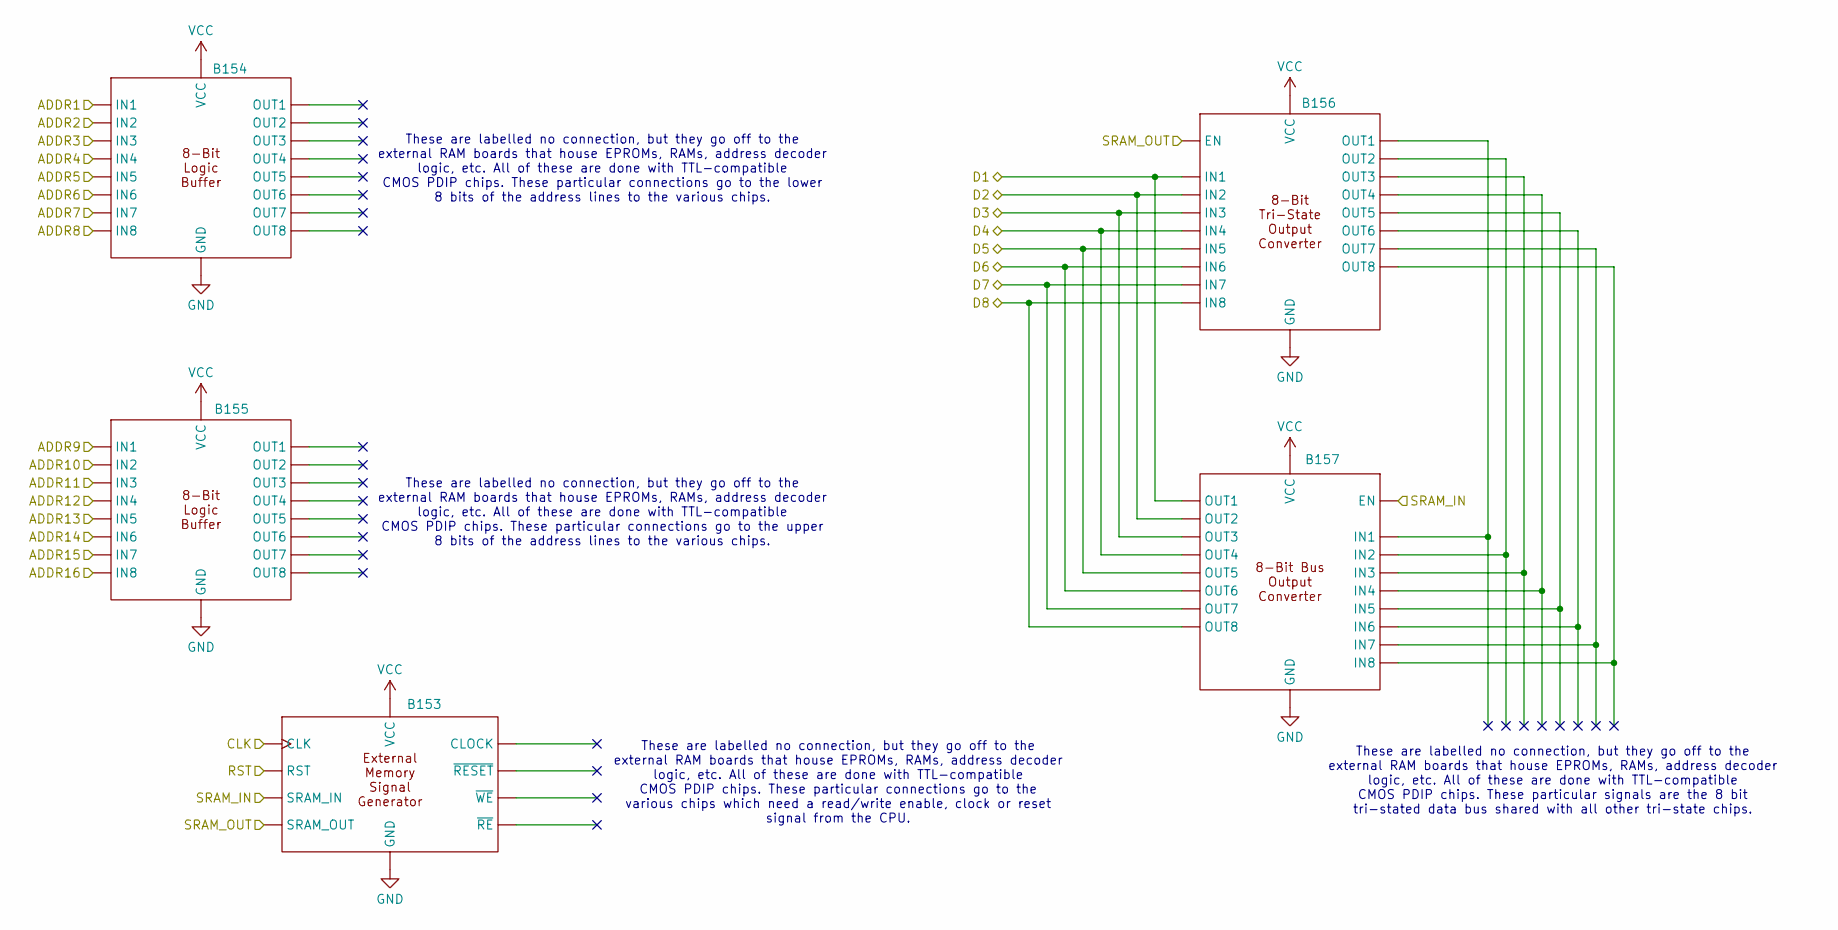
[picture p35: schematic SRAM Interface.kicad_sch]

Parts:
B153, B154, B155, B156, B157: (no value)

Connections:
ADDR1: B154.
ADDR2: B154.
ADDR3: B154.
ADDR4: B154.
ADDR5: B154.
ADDR6: B154.
ADDR7: B154.
ADDR8: B154.
ADDR9: B155.
ADDR10: B155.
ADDR11: B155.
ADDR12: B155.
ADDR13: B155.
ADDR14: B155.
ADDR15: B155.
ADDR16: B155.
CLK: B153.
D1: B156., B157.
D2: B156., B157.
D3: B156., B157.
D4: B156., B157.
D5: B156., B157.
D6: B156., B157.
D7: B156., B157.
D8: B156., B157.
GND: B153., B154., B155., B156., B157.
unnamed: B156., B157.
RST: B153.
SRAM_IN: B153., B157.
SRAM_OUT: B153., B156.
VCC: B153., B154., B155., B156., B157.

Notes on the sheet:
These are labelled no connection, but they go off to the external RAM boards that house EPROMs, RAMs, address decoder logic, etc. All of these are done with TTL-compatible CMOS PDIP chips. These particular connections go to the various chips which need a read/write enable, clock or reset signal fro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
These are labelled no connection, but they go off to the external RAM boards that house EPROMs, RAMs, address decoder logic, etc. All of these are done with TTL-compatible CMOS PDIP chips. These particular signals are the 8 bit tri-stated data bus shared with all other tri-state chips.
These are labelled no connection, but they go off to the external RAM boards that house EPROMs, RAMs, address decoder logic, etc. All of these are done with TTL-compatible CMOS PDIP chips. These particular connections go to the lower 8 bits of the address lines to the various chips.
These are labelled no connection, but they go off to the external RAM boards that house EPROMs, RAMs, address decoder logic, etc. All of these are done with TTL-compatible CMOS PDIP chips. These particular connections go to the upper 8 bits of the address lines to the various chips.
