pennyarcade/minidragon/schematics/Layout/Shift and Compare.kicad_sch

## KiCad design schematics/Layout/Shift and Compare.kicad_sch (2026-05-20)

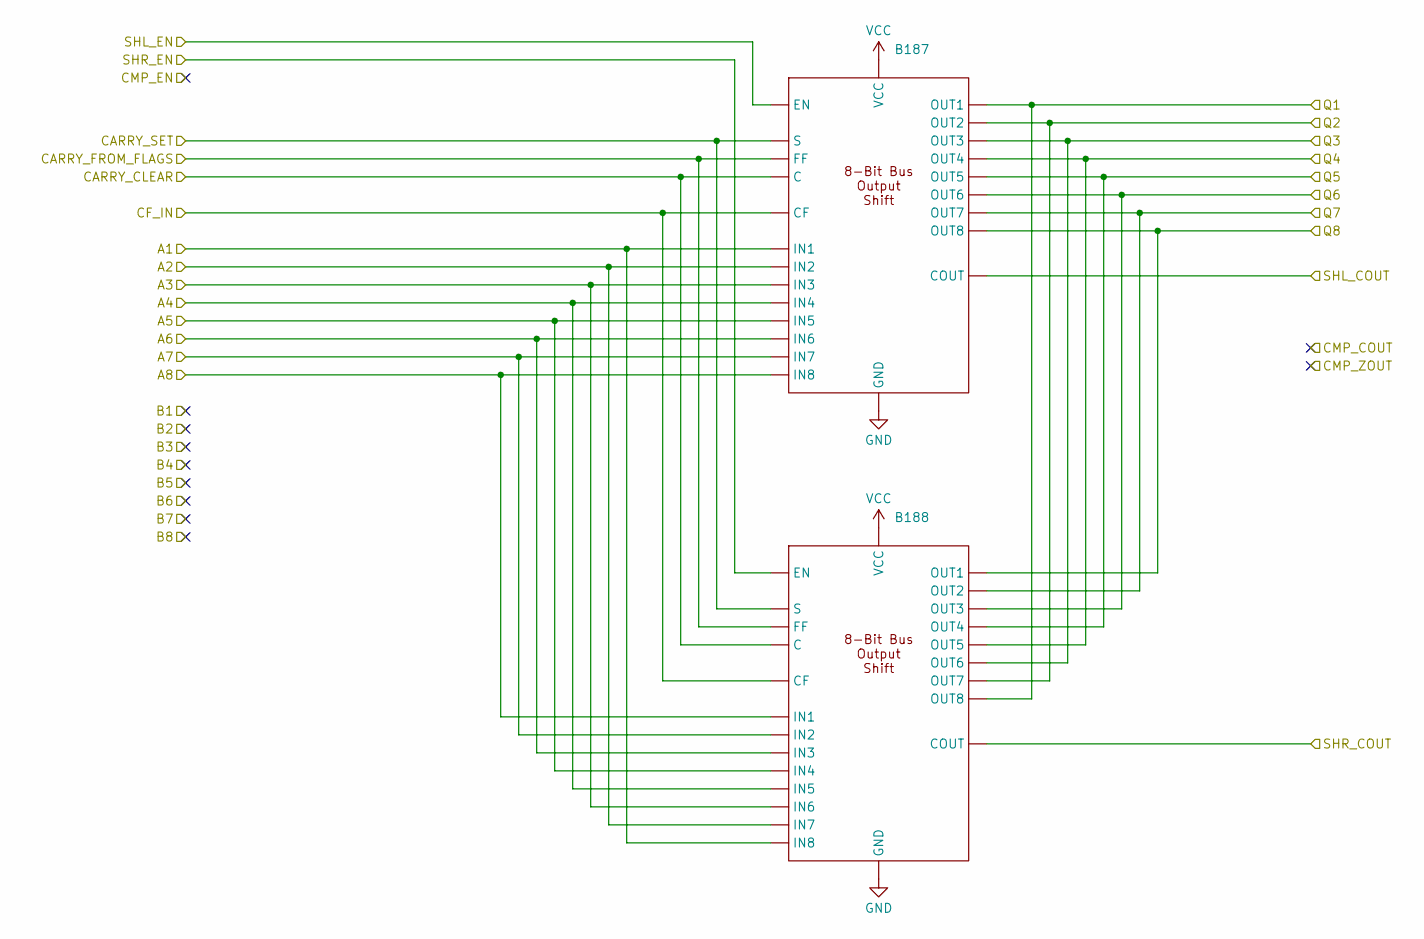
[picture p36: schematic Shift and Compare.kicad_sch]

Parts:
B187, B188: (no value)

Connections:
A1: B187., B188.
A2: B187., B188.
A3: B187., B188.
A4: B187., B188.
A5: B187., B188.
A6: B187., B188.
A7: B187., B188.
A8: B187., B188.
CARRY_CLEAR: B187., B188.
CARRY_FROM_FLAGS: B187., B188.
CARRY_SET: B187., B188.
CF_IN: B187., B188.
GND: B187., B188.
Q1: B187., B188.
Q2: B187., B188.
Q3: B187., B188.
Q4: B187., B188.
Q5: B187., B188.
Q6: B187., B188.
Q7: B187., B188.
Q8: B187., B188.
SHL_COUT: B187.
SHL_EN: B187.
SHR_COUT: B188.
SHR_EN: B188.
VCC: B187., B188.
