pennyarcade/minidragon/schematics/Layout/U Register.kicad_sch

## KiCad design schematics/Layout/U Register.kicad_sch (2026-05-20)

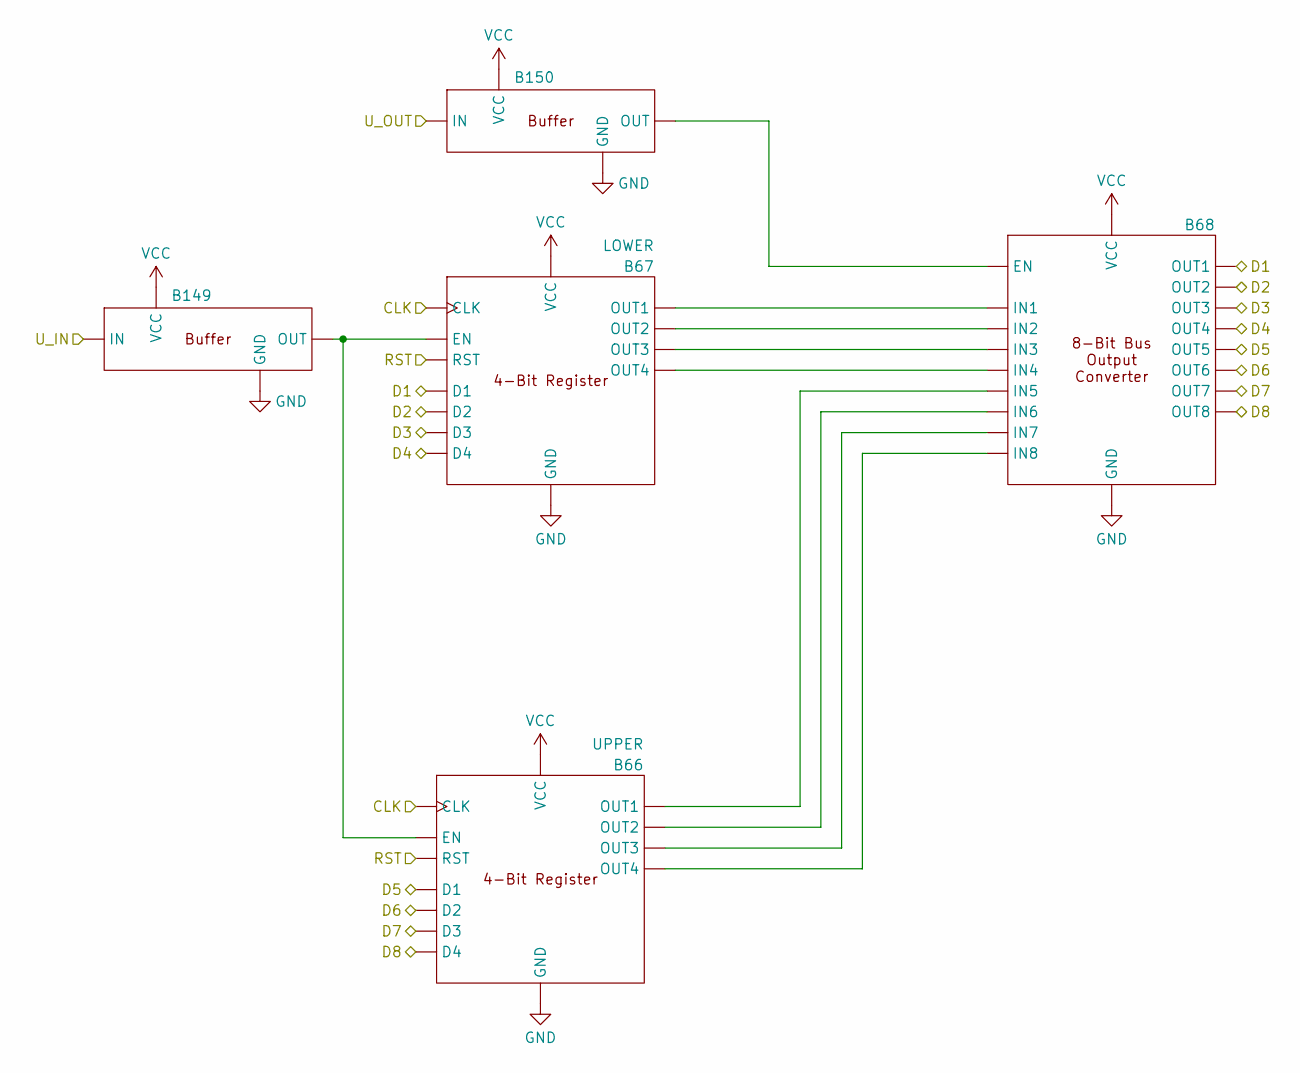
[picture p37: schematic U Register.kicad_sch]

Parts:
B66: UPPER
B67: LOWER
B68, B149, B150: (no value)

Connections:
CLK: B66., B67.
D1: B67., B68.
D2: B67., B68.
D3: B67., B68.
D4: B67., B68.
D5: B66., B68.
D6: B66., B68.
D7: B66., B68.
D8: B66., B68.
GND: B66., B67., B68., B149., B150.
unnamed: B66., B68.
unnamed: B67., B68.
unnamed: B66., B67., B149.
unnamed: B68., B150.
RST: B66., B67.
U_IN: B149.
U_OUT: B150.
VCC: B66., B67., B68., B149., B150.
